claybford/ergothwack/drafts/beta/PXL_20240225_135907573.jpg

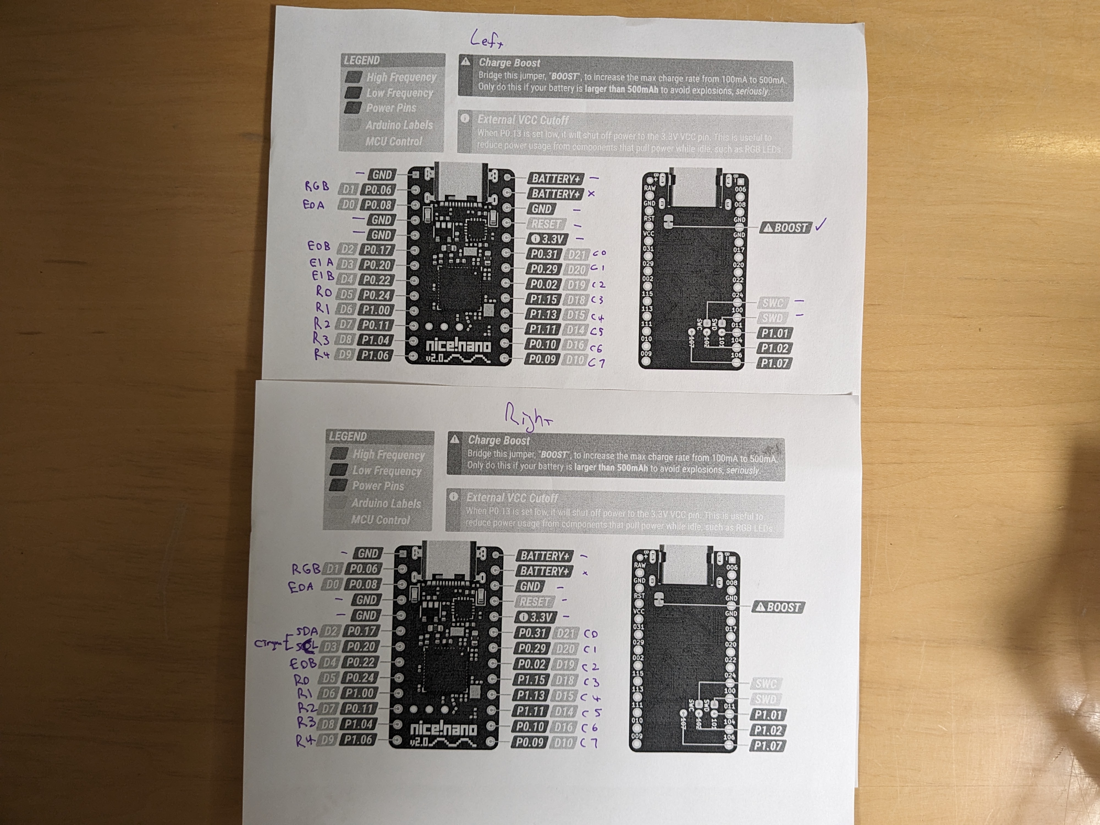
drafts/beta/PXL_20240225_135907573.jpg
