claybford/ergothwack/drafts/beta/PXL_20240225_155118894.jpg

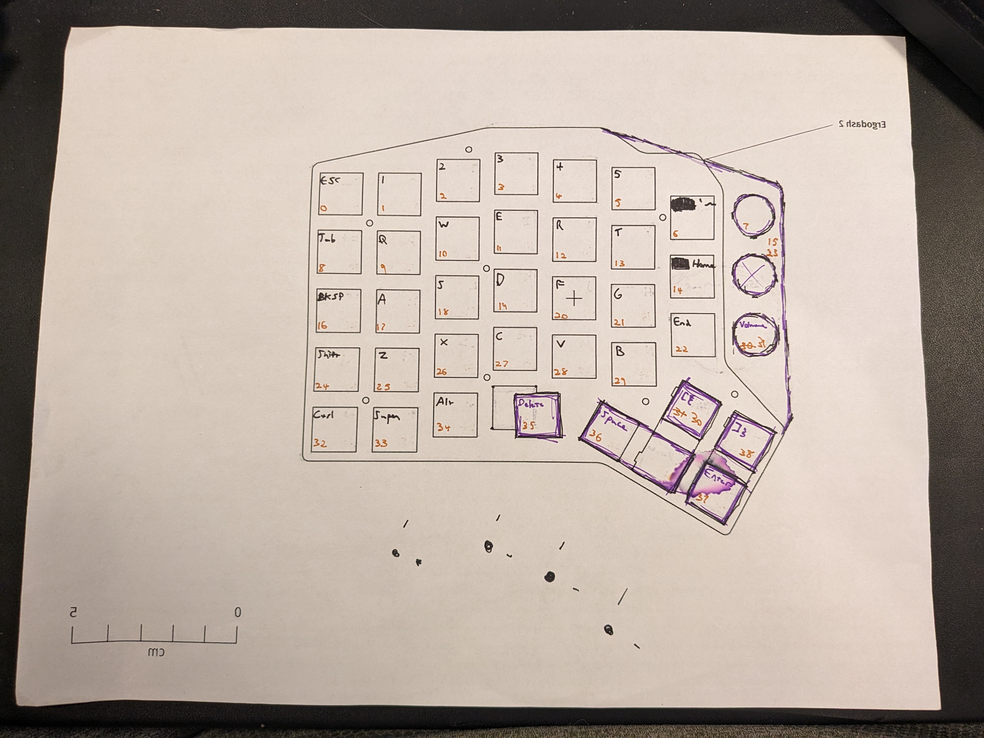
drafts/beta/PXL_20240225_155118894.jpg
