claybford/ergothwack/drafts/beta/PXL_20240225_155126803.jpg

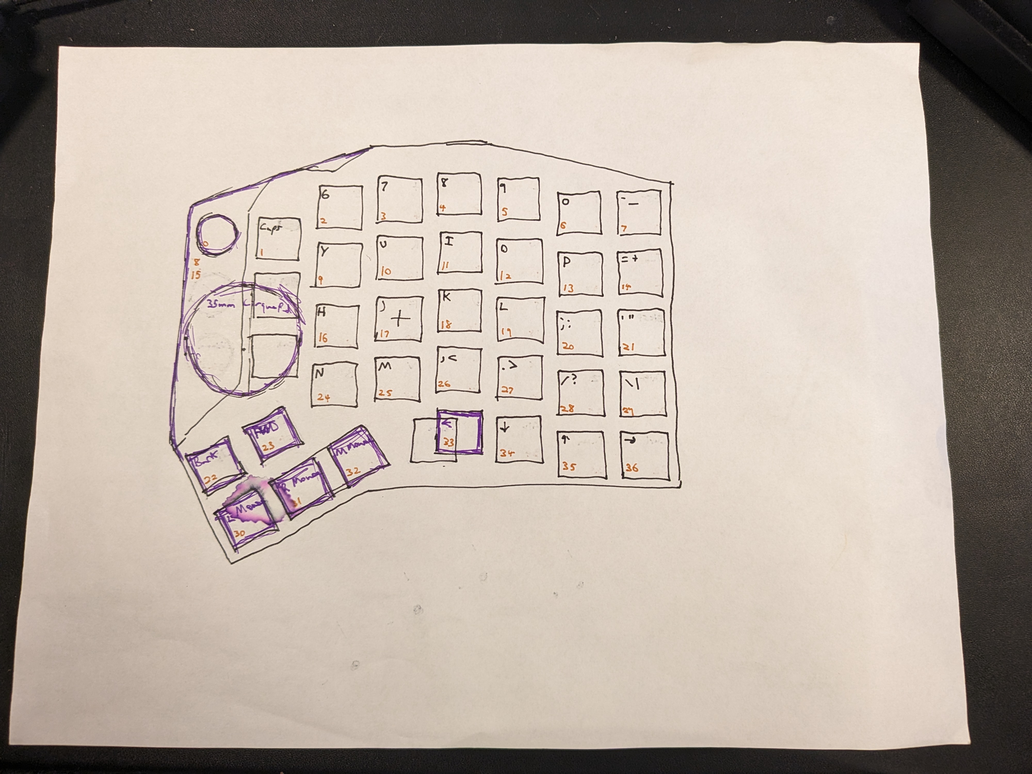
drafts/beta/PXL_20240225_155126803.jpg
