claybford/ergothwack/photos/beta/PXL_20240208_200405498.jpg

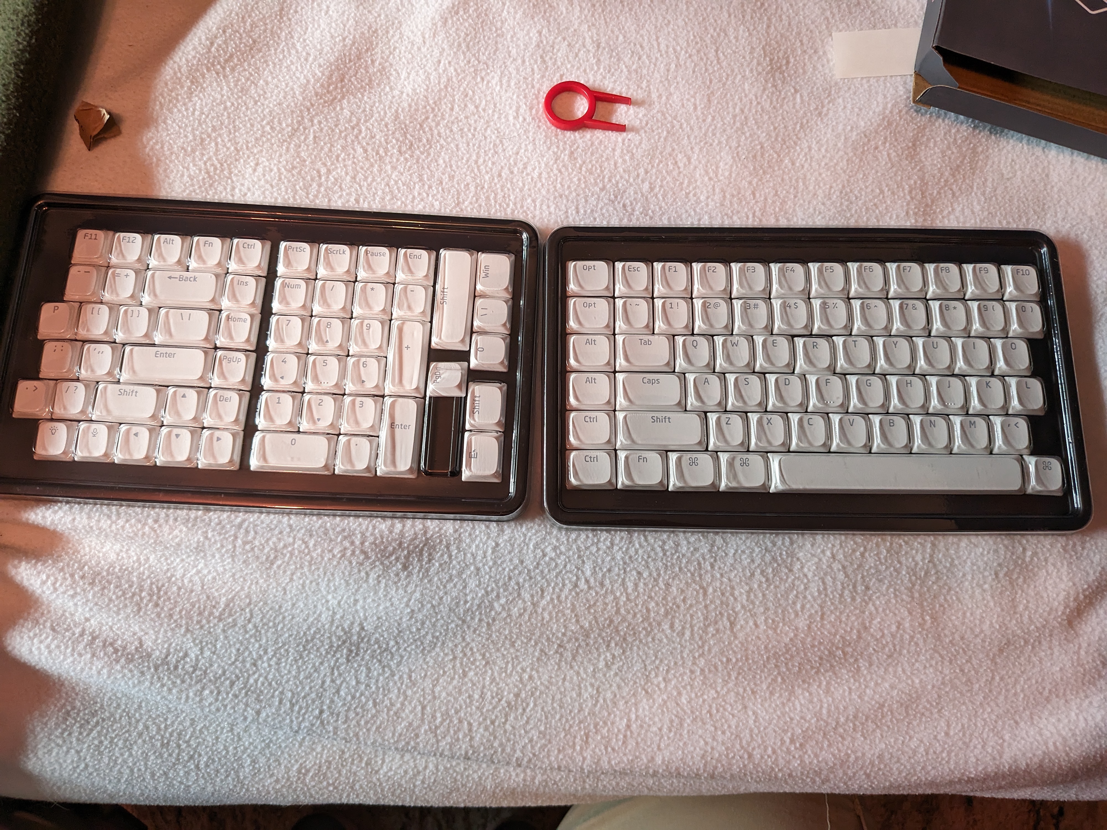
photos/beta/PXL_20240208_200405498.jpg
