claybford/ergothwack/photos/beta/PXL_20240208_202022478.jpg

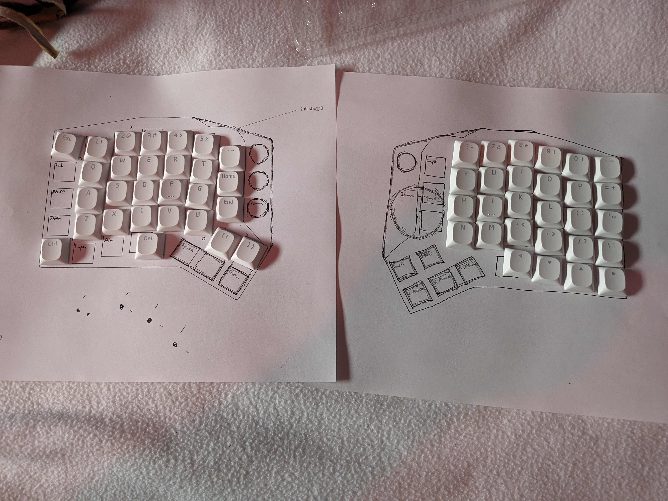
photos/beta/PXL_20240208_202022478.jpg
