claybford/ergothwack/photos/beta/PXL_20240215_032502192.jpg

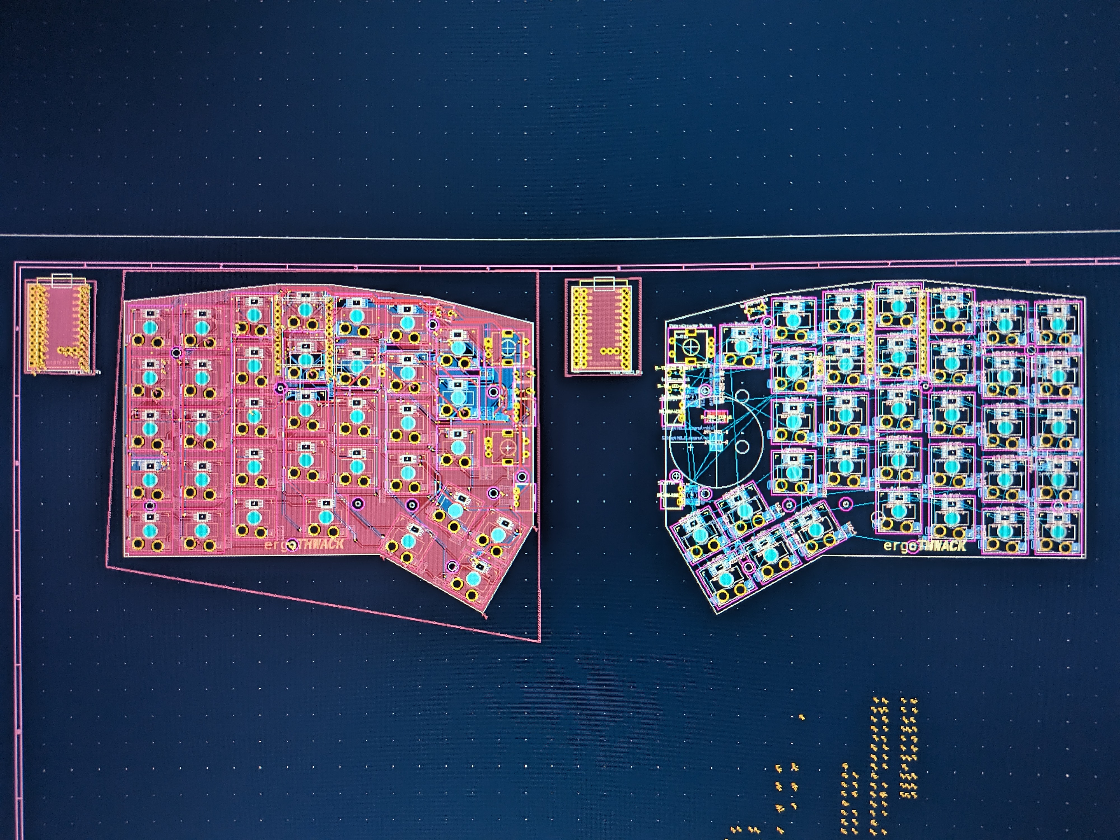
photos/beta/PXL_20240215_032502192.jpg
