claybford/ergothwack/photos/beta/PXL_20240216_200051244~2.jpg

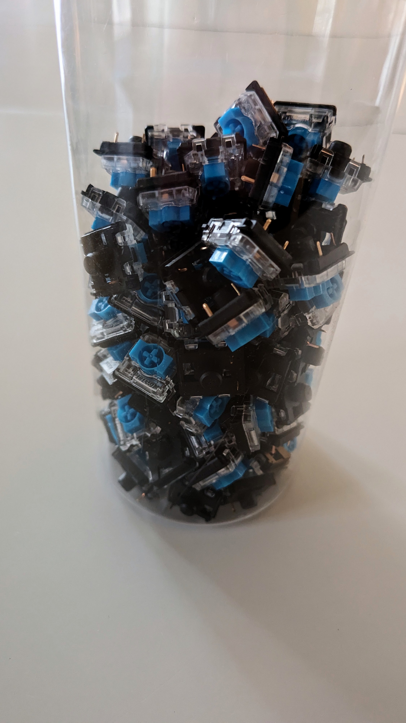
photos/beta/PXL_20240216_200051244~2.jpg
