claybford/ergothwack/photos/beta/PXL_20240217_183212310~2.jpg

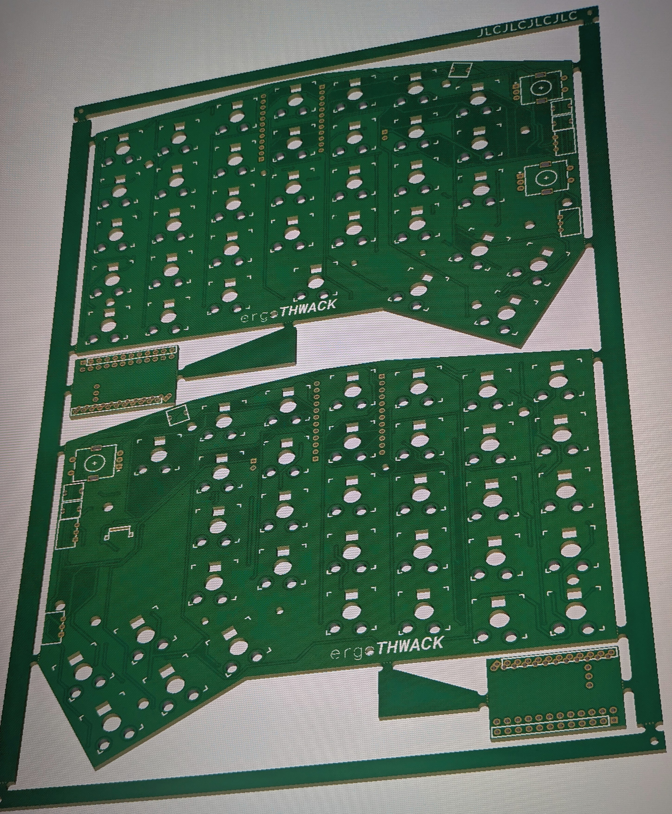
photos/beta/PXL_20240217_183212310~2.jpg
