claybford/ergothwack/photos/beta/PXL_20240222_214427850.jpg

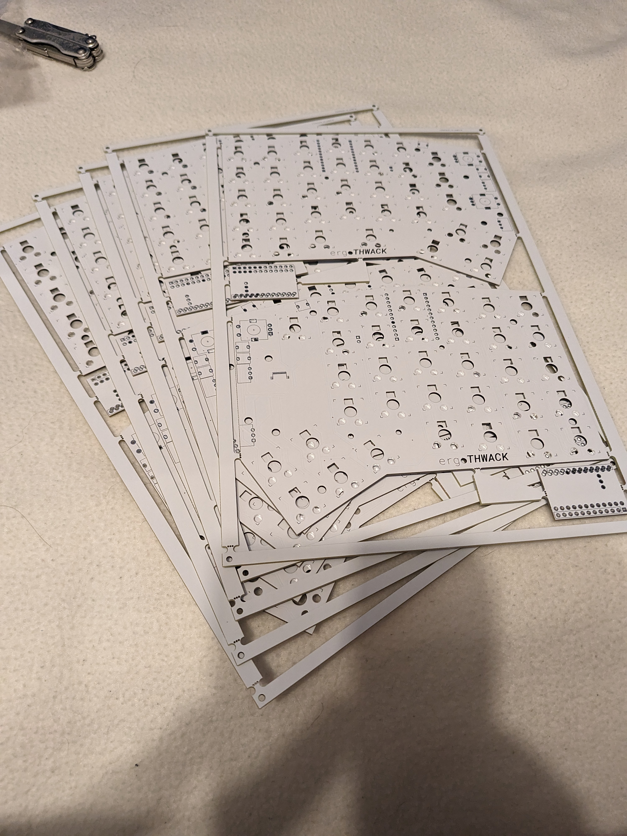
photos/beta/PXL_20240222_214427850.jpg
