claybford/ergothwack/photos/beta/PXL_20240222_214445857.jpg

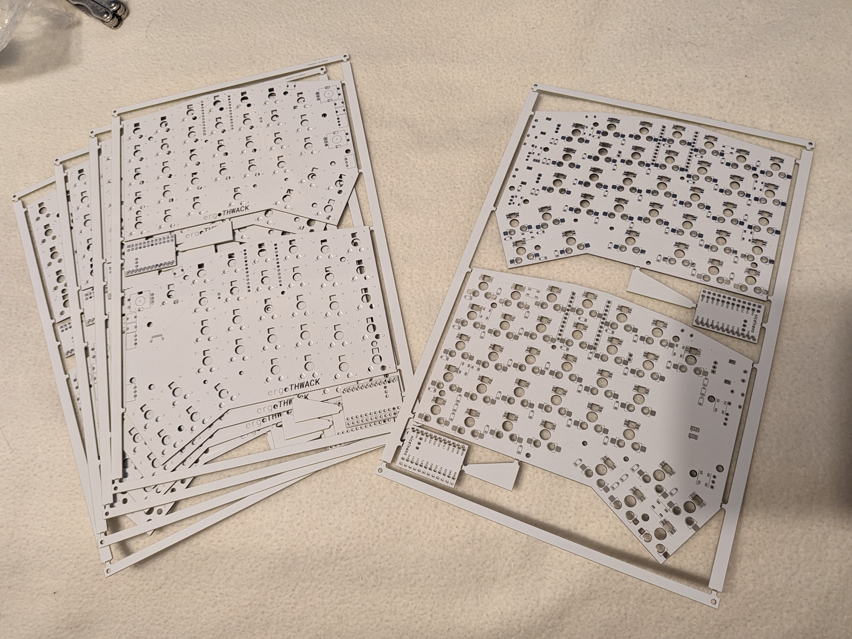
photos/beta/PXL_20240222_214445857.jpg
