claybford/ergothwack/photos/beta/PXL_20240222_214501451.jpg

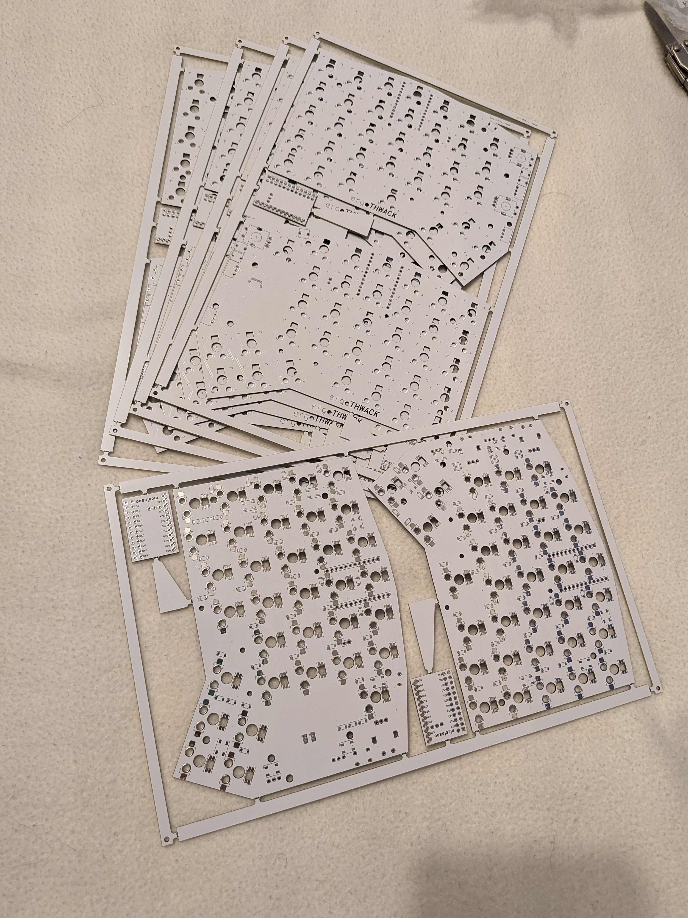
photos/beta/PXL_20240222_214501451.jpg
