claybford/ergothwack/photos/beta/PXL_20240222_214855161.jpg

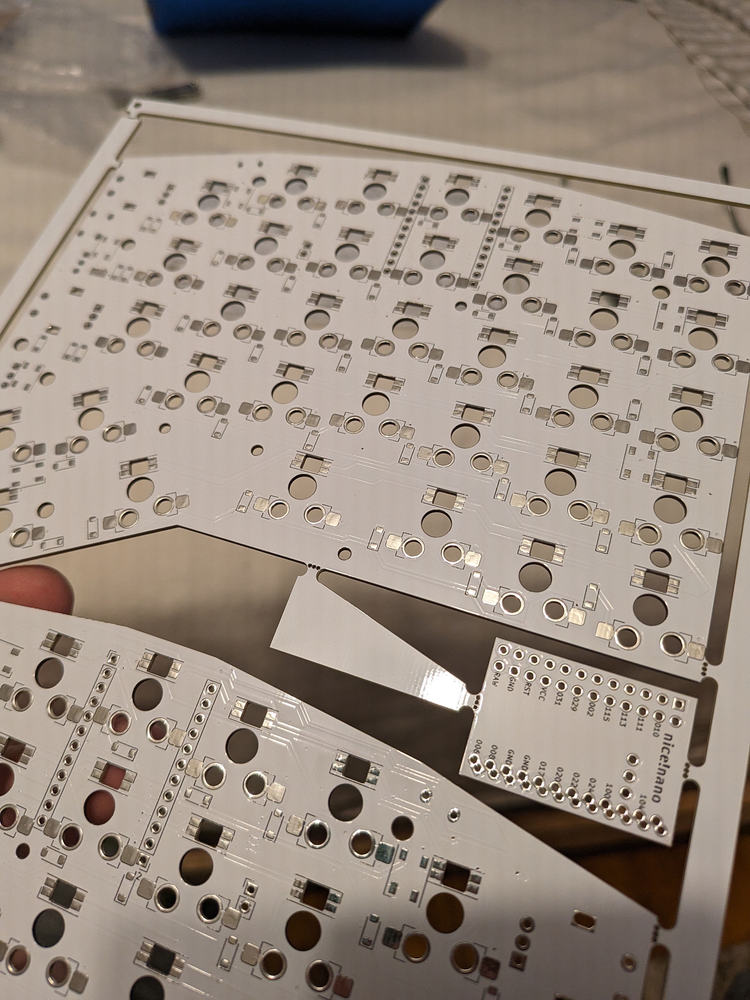
photos/beta/PXL_20240222_214855161.jpg
