claybford/ergothwack/photos/beta/PXL_20240222_214902118.jpg

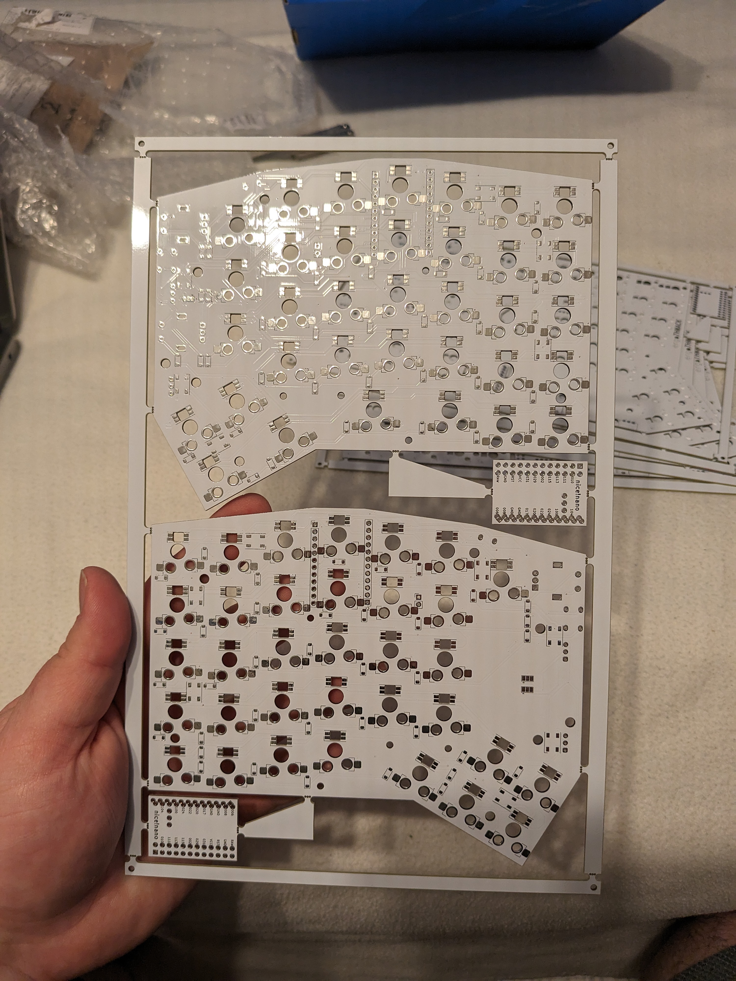
photos/beta/PXL_20240222_214902118.jpg
