claybford/ergothwack/photos/beta/PXL_20240222_214908877.jpg

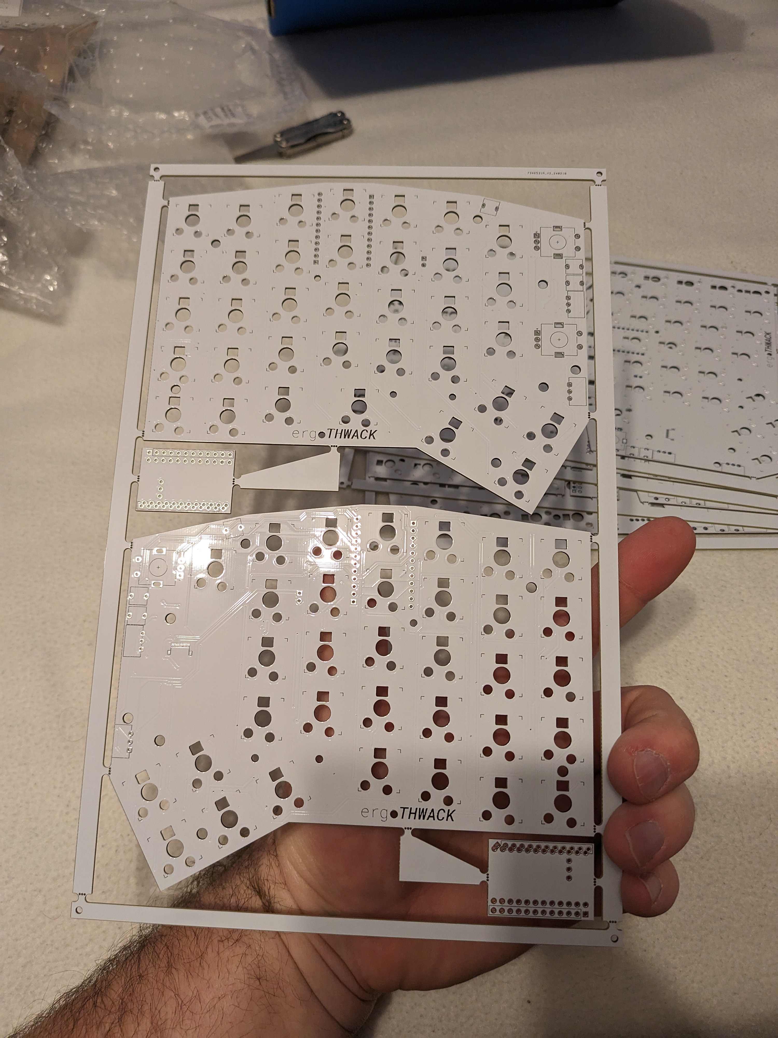
photos/beta/PXL_20240222_214908877.jpg
