claybford/ergothwack/photos/beta/PXL_20240222_215357096.jpg

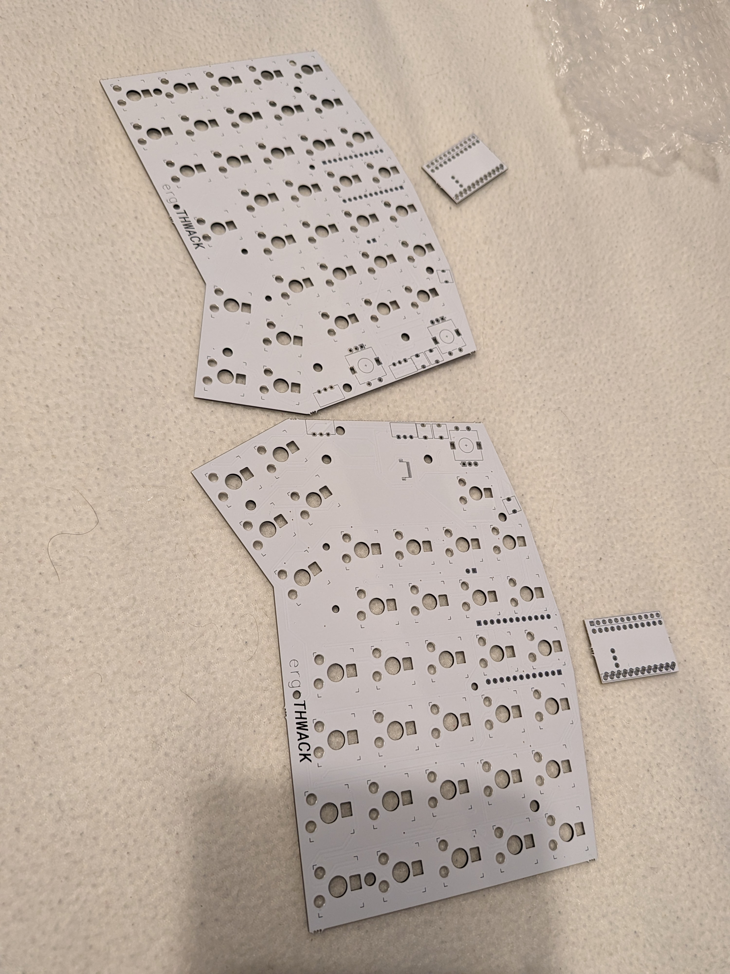
photos/beta/PXL_20240222_215357096.jpg
