claybford/ergothwack/photos/beta/PXL_20240224_054337741.jpg

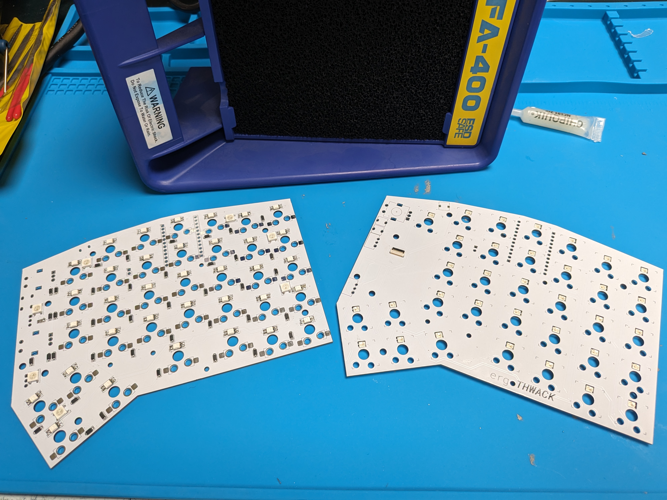
photos/beta/PXL_20240224_054337741.jpg
