claybford/ergothwack/photos/beta/PXL_20240224_054445099.jpg

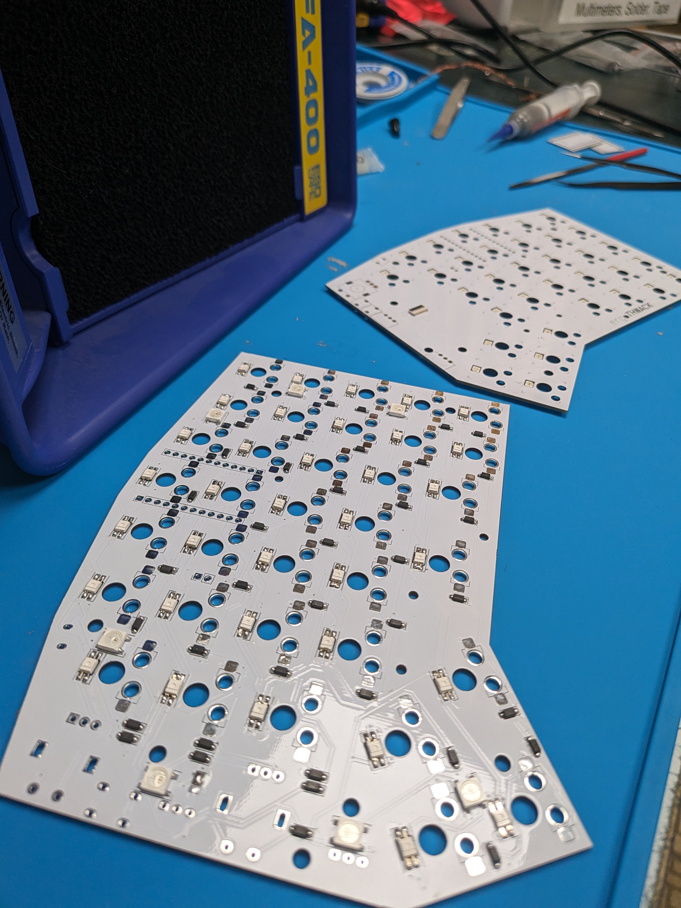
photos/beta/PXL_20240224_054445099.jpg
