claybford/ergothwack/photos/beta/PXL_20240224_054820994.jpg

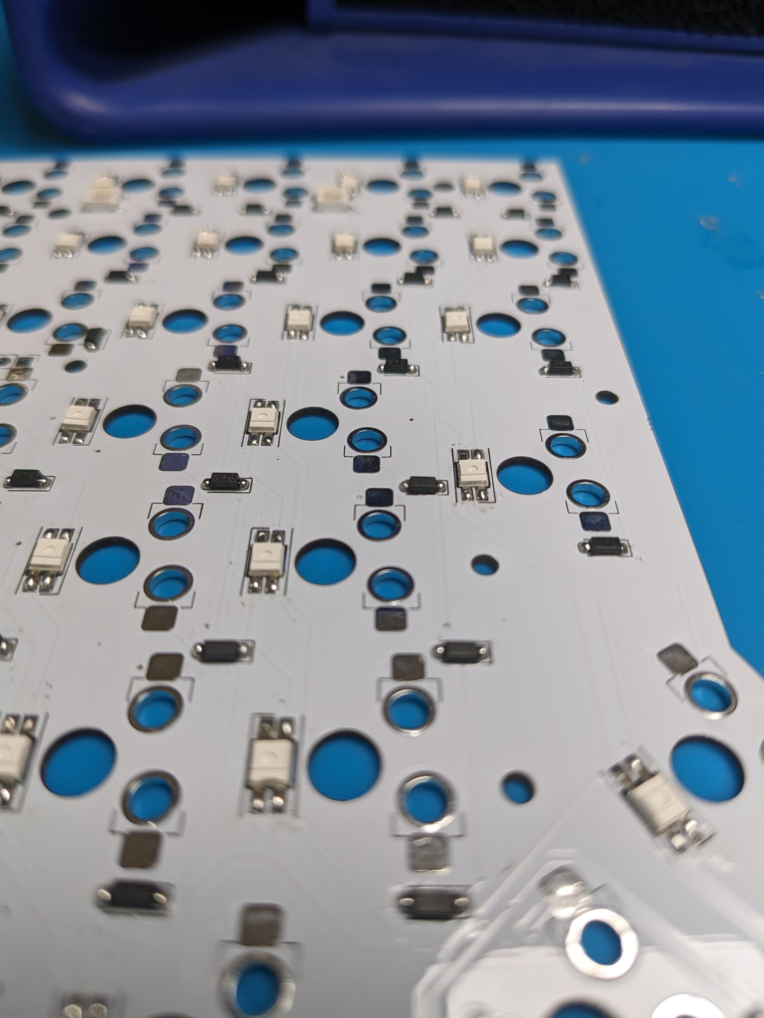
photos/beta/PXL_20240224_054820994.jpg
