claybford/ergothwack/photos/beta/PXL_20240227_215155675~2.jpg

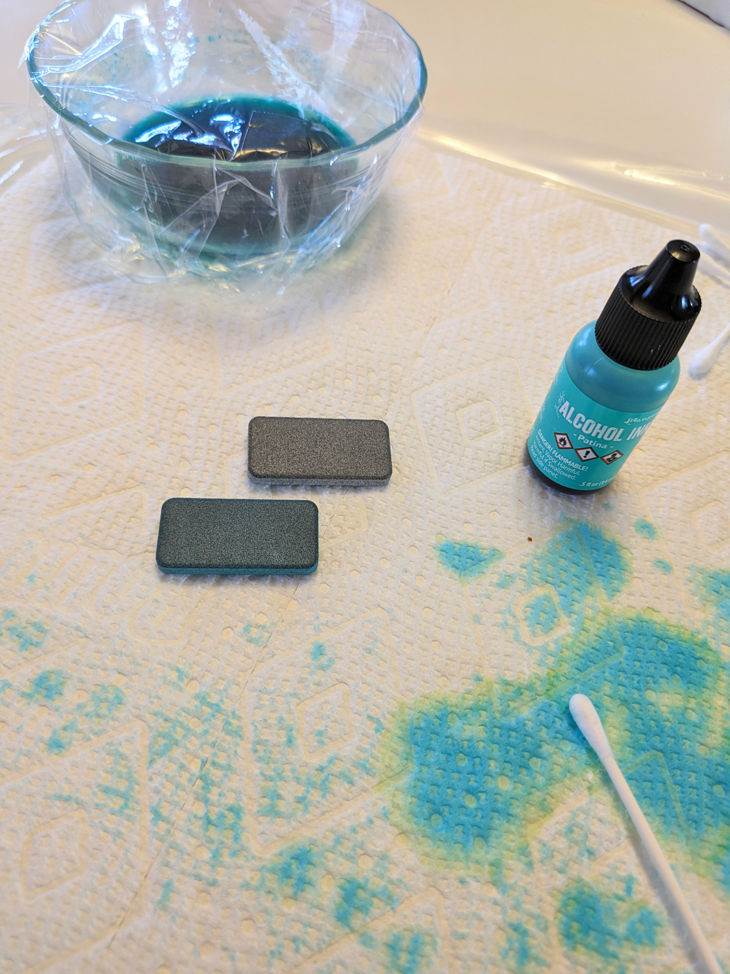
photos/beta/PXL_20240227_215155675~2.jpg
