claybford/ergothwack/photos/beta/PXL_20240301_024840404.jpg

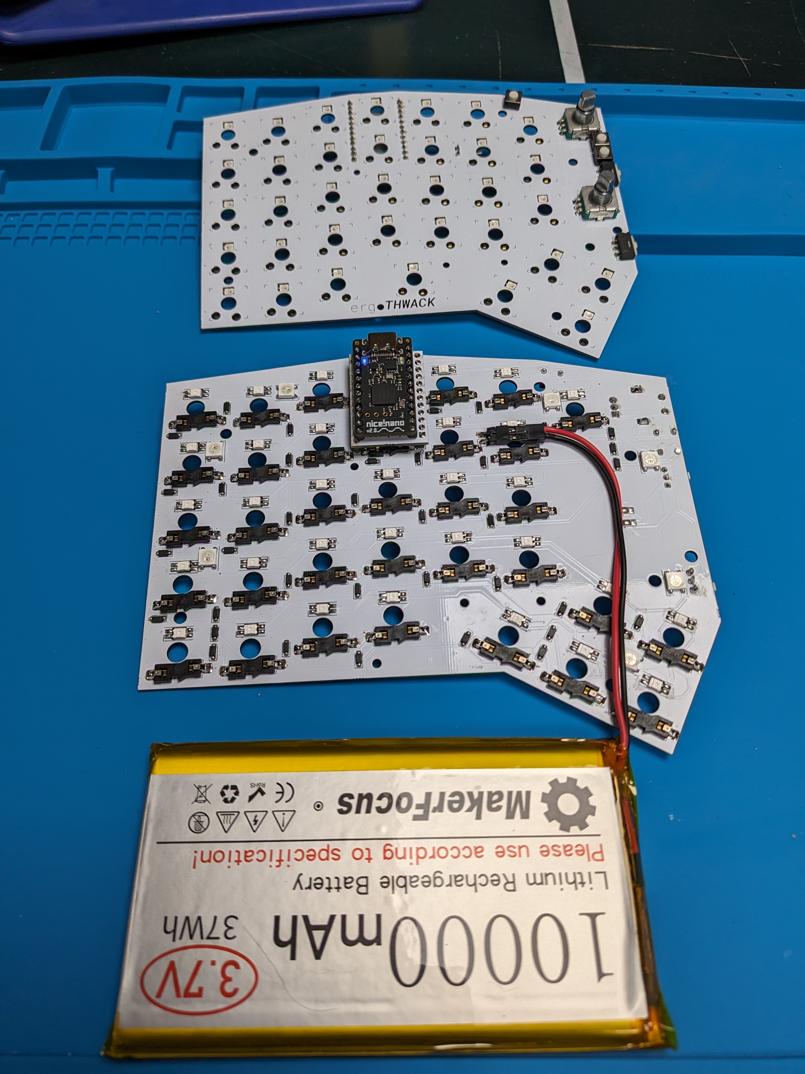
photos/beta/PXL_20240301_024840404.jpg
