claybford/ergothwack/photos/beta/PXL_20240301_025422989.jpg

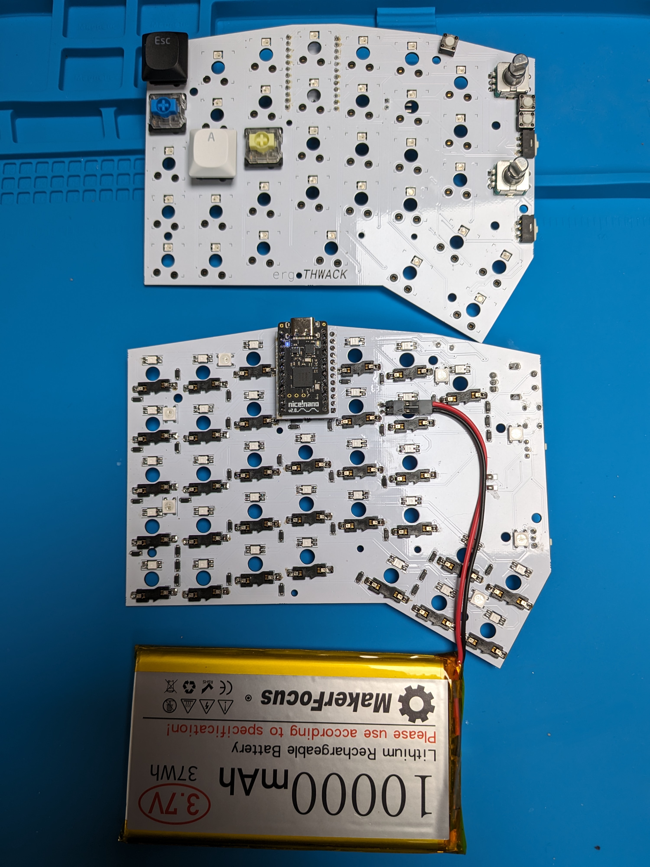
photos/beta/PXL_20240301_025422989.jpg
