claybford/ergothwack/photos/beta/PXL_20240304_221708577.jpg

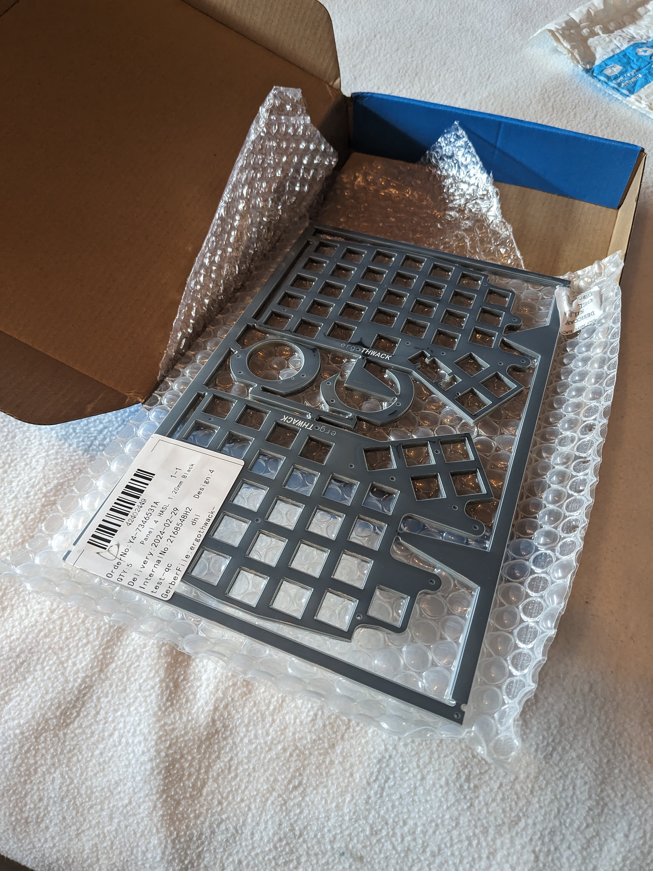
photos/beta/PXL_20240304_221708577.jpg
