claybford/ergothwack/photos/beta/PXL_20240305_060824923.jpg

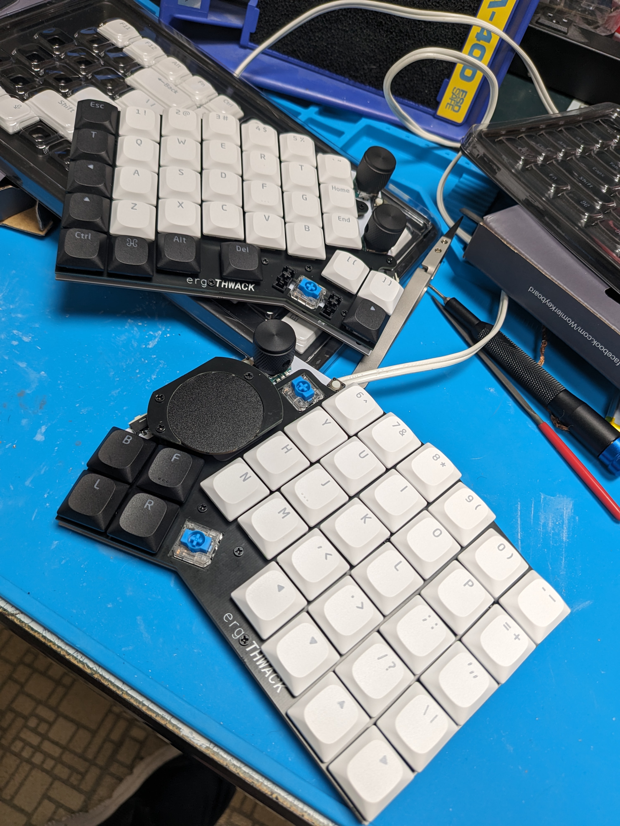
photos/beta/PXL_20240305_060824923.jpg
