claybford/ergothwack/photos/beta/PXL_20240307_211200613.jpg

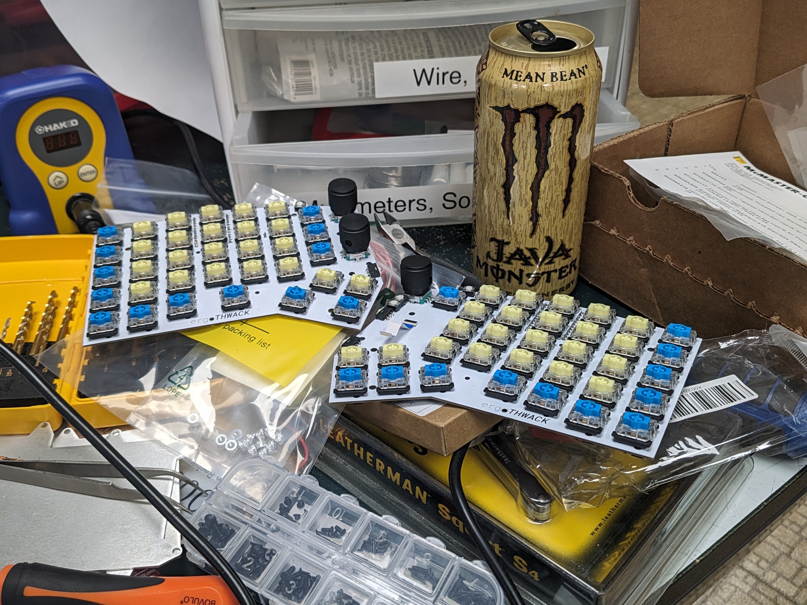
photos/beta/PXL_20240307_211200613.jpg
