claybford/ergothwack/photos/beta/PXL_20240307_211225900.jpg

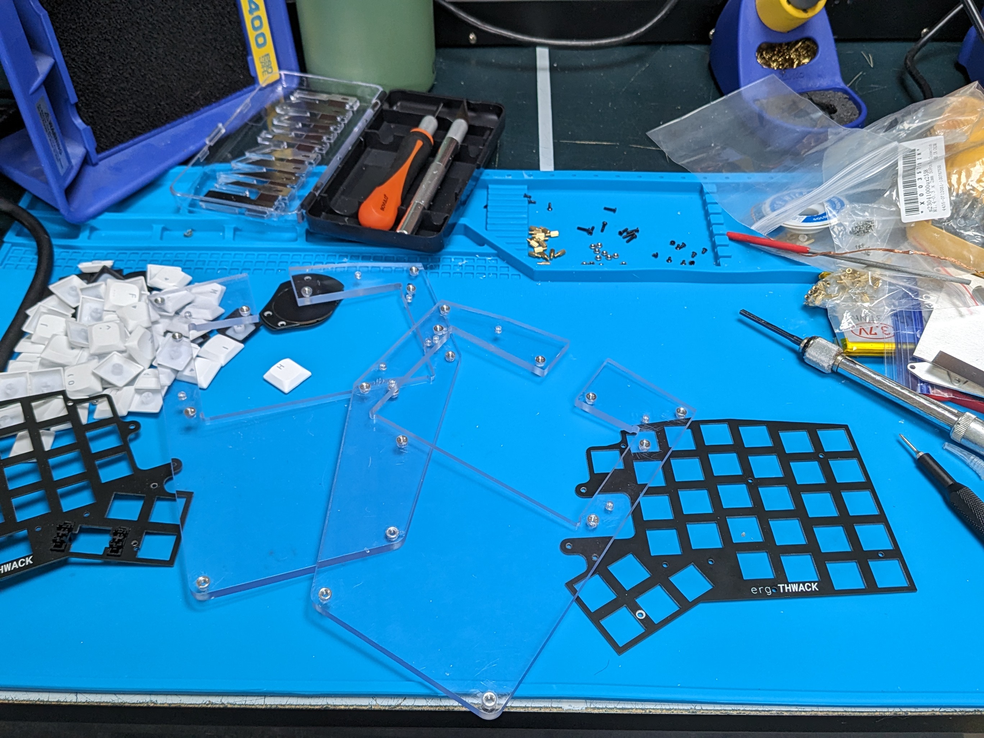
photos/beta/PXL_20240307_211225900.jpg
