claybford/ergothwack/photos/beta/PXL_20240307_215815214.jpg

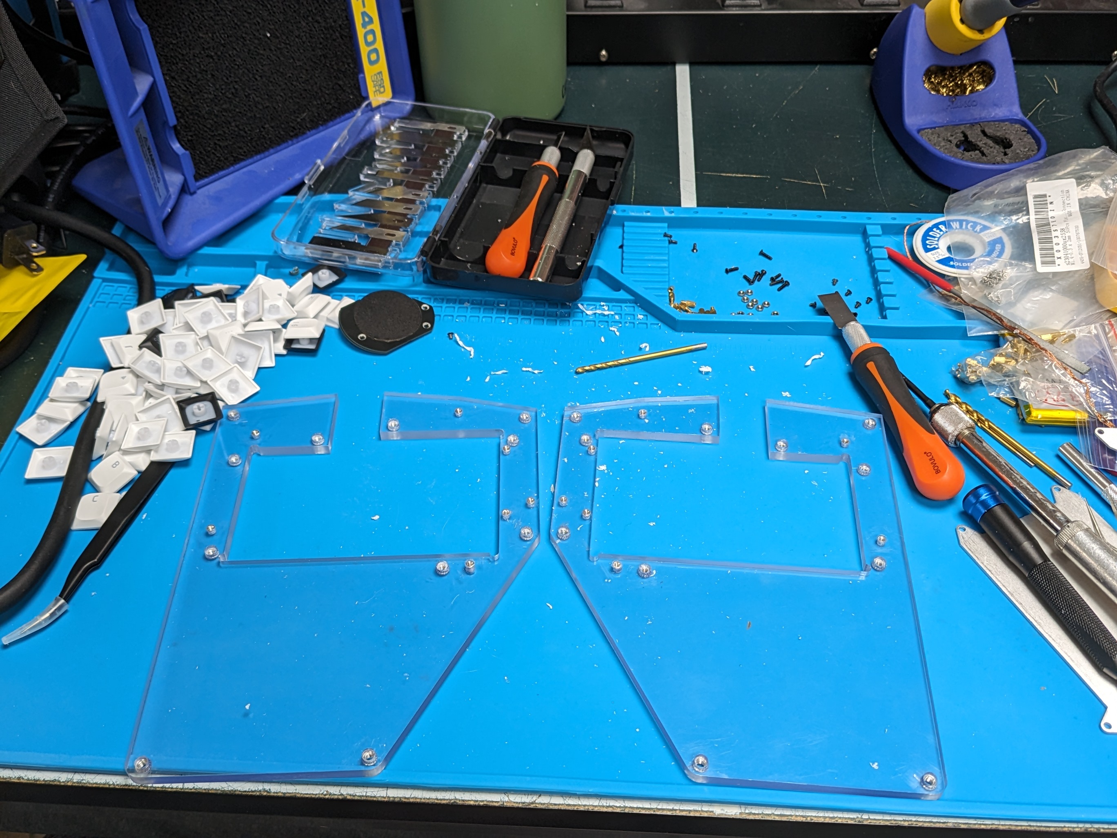
photos/beta/PXL_20240307_215815214.jpg
