claybford/ergothwack/photos/beta/PXL_20240308_015111697.jpg

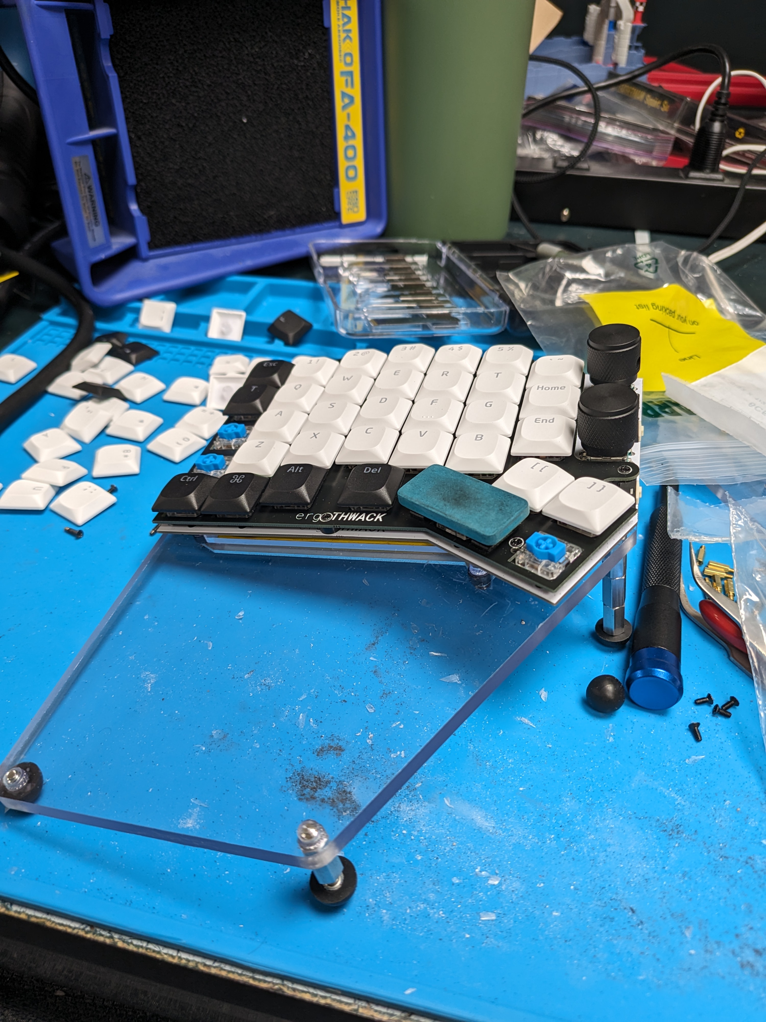
photos/beta/PXL_20240308_015111697.jpg
