claybford/ergothwack/photos/beta/PXL_20240308_015728550.jpg

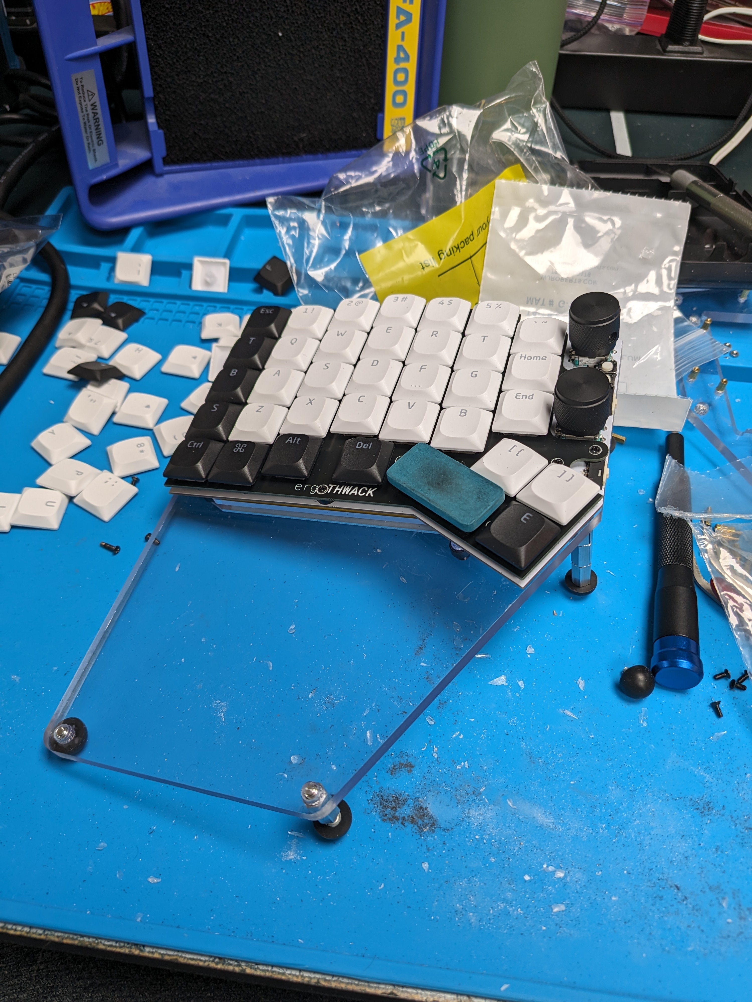
photos/beta/PXL_20240308_015728550.jpg
