claybford/ergothwack/photos/beta/PXL_20240309_044629597.jpg

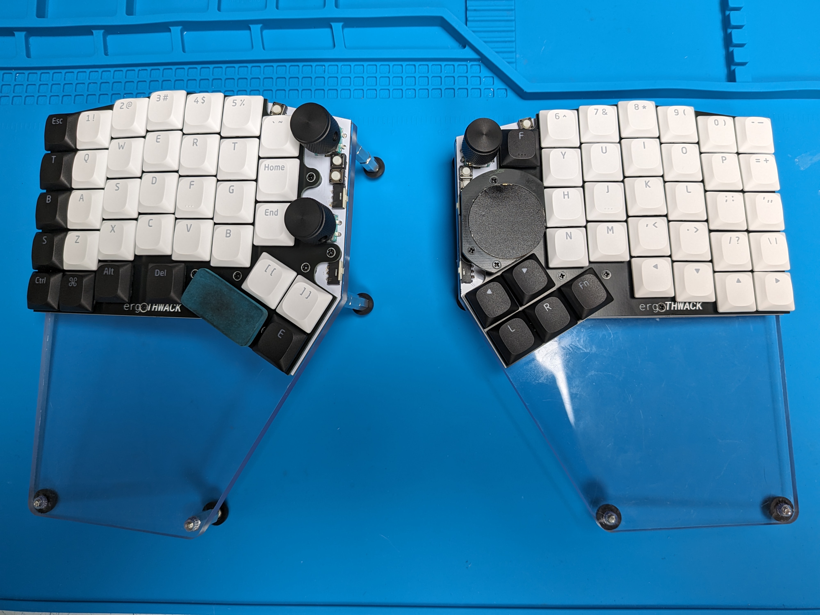
photos/beta/PXL_20240309_044629597.jpg
