claybford/ergothwack/photos/beta/PXL_20240310_044820362.jpg

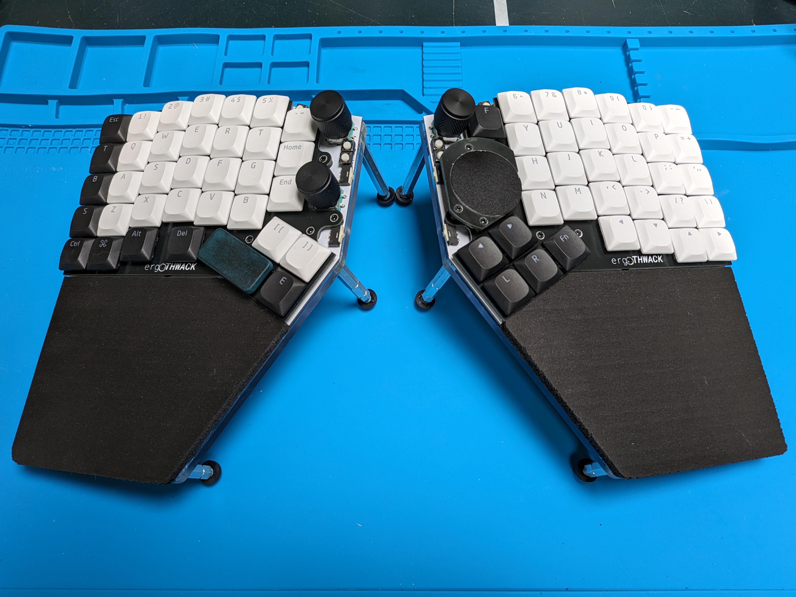
photos/beta/PXL_20240310_044820362.jpg
