claybford/ergothwack/photos/beta/PXL_20240316_183658946.jpg

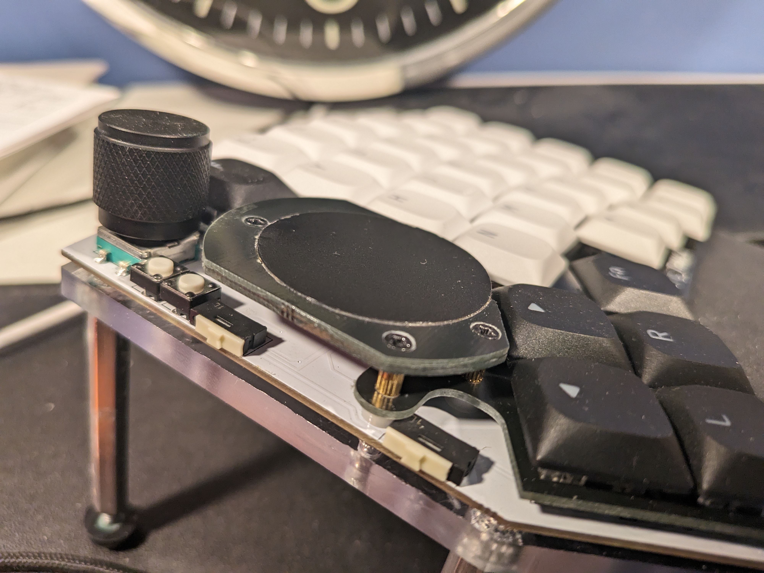
photos/beta/PXL_20240316_183658946.jpg
