claybford/ergothwack/photos/beta/PXL_20240316_183718555.jpg

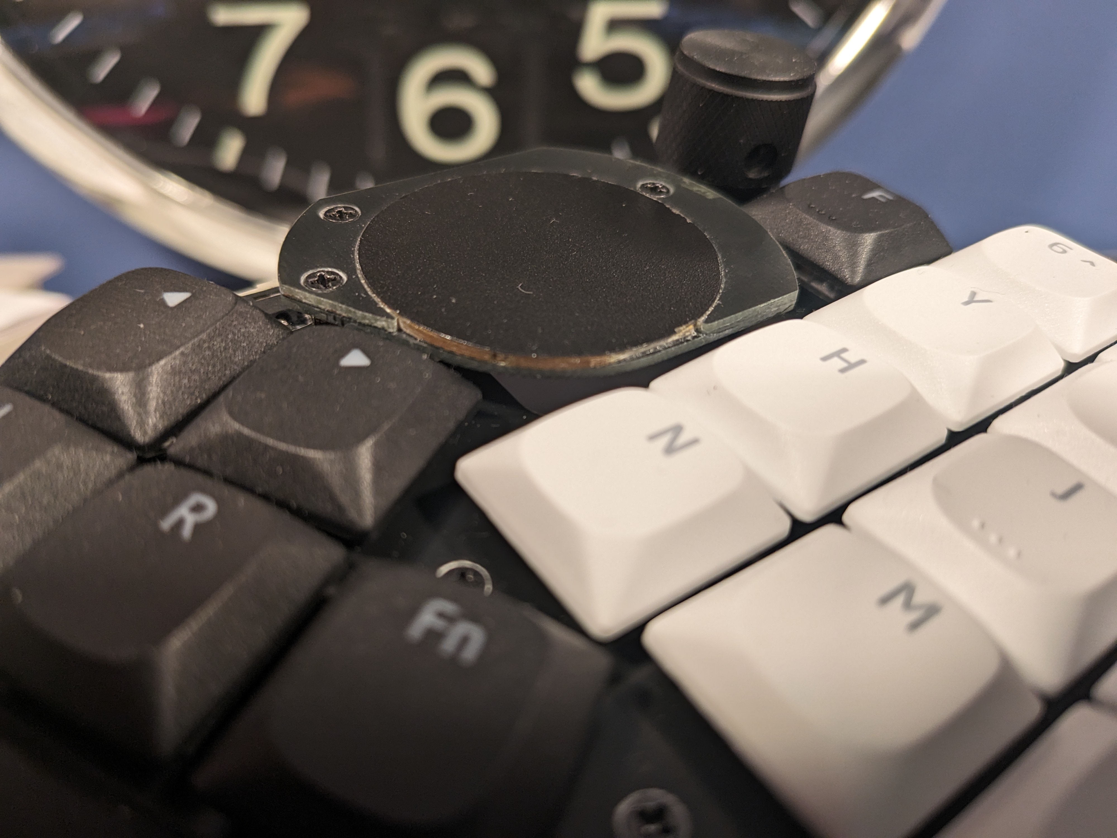
photos/beta/PXL_20240316_183718555.jpg
