claybford/ergothwack/photos/beta/PXL_20240317_012301412.jpg

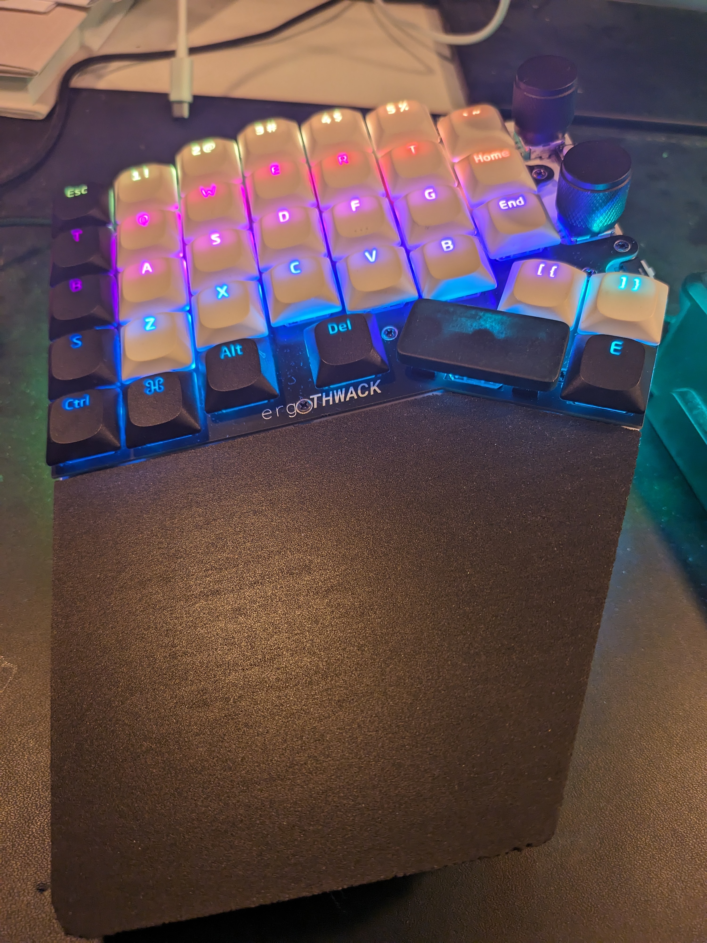
photos/beta/PXL_20240317_012301412.jpg
