claybford/ergothwack/photos/beta/PXL_20240317_012305706.jpg

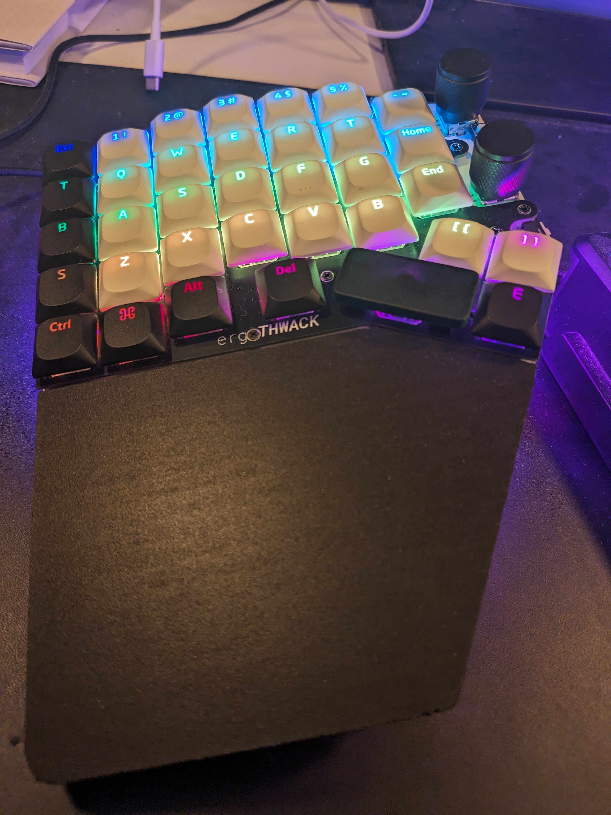
photos/beta/PXL_20240317_012305706.jpg
