claybford/ergothwack/photos/beta/PXL_20240321_230017577.jpg

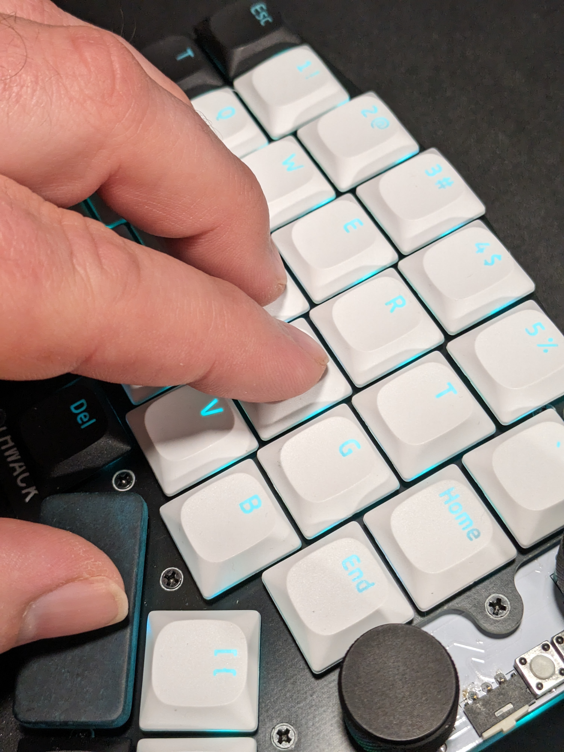
photos/beta/PXL_20240321_230017577.jpg
