claybford/ergothwack/reference documents/gateron low profile stabilizer.png

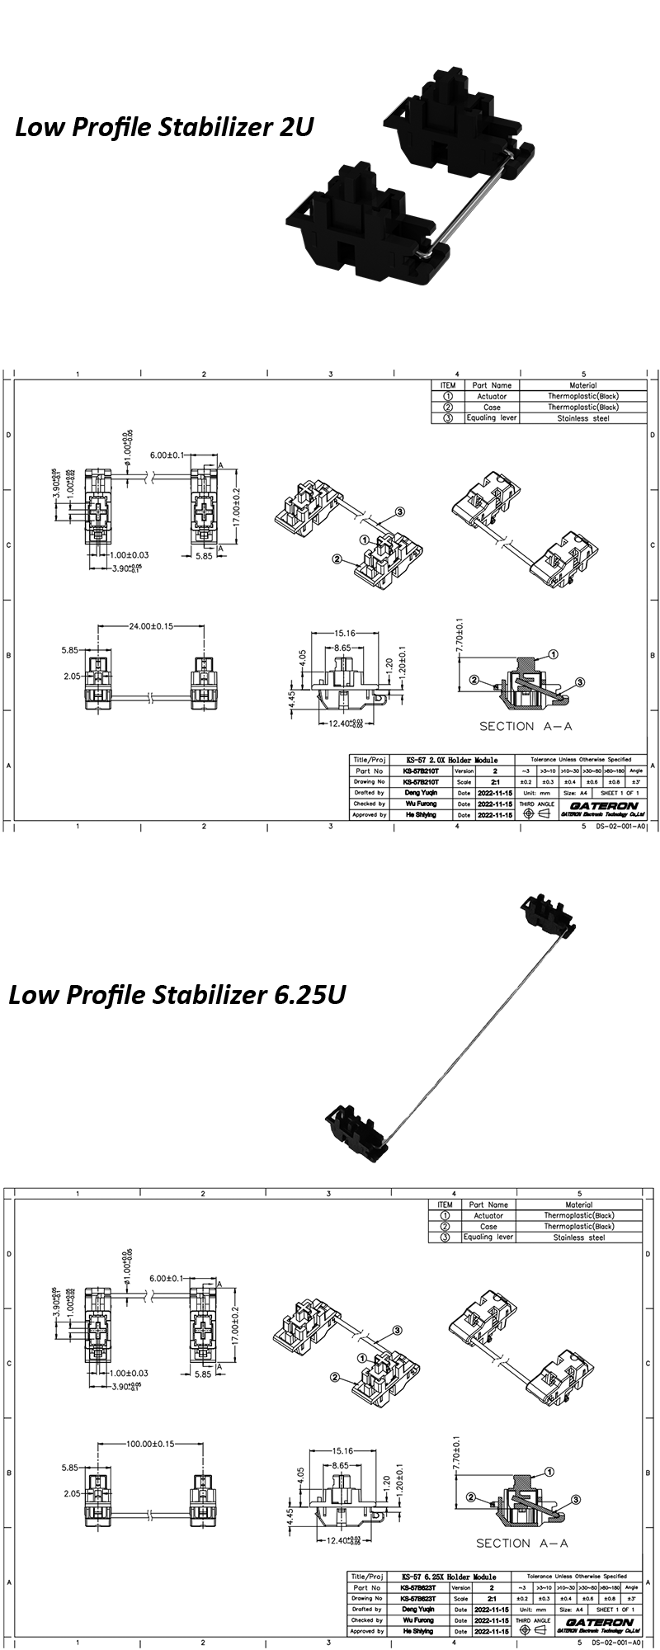
reference documents/gateron low profile stabilizer.png
