claybford/ergothwack/reference documents/Gateron low-profile hot swap socket diagram.webp

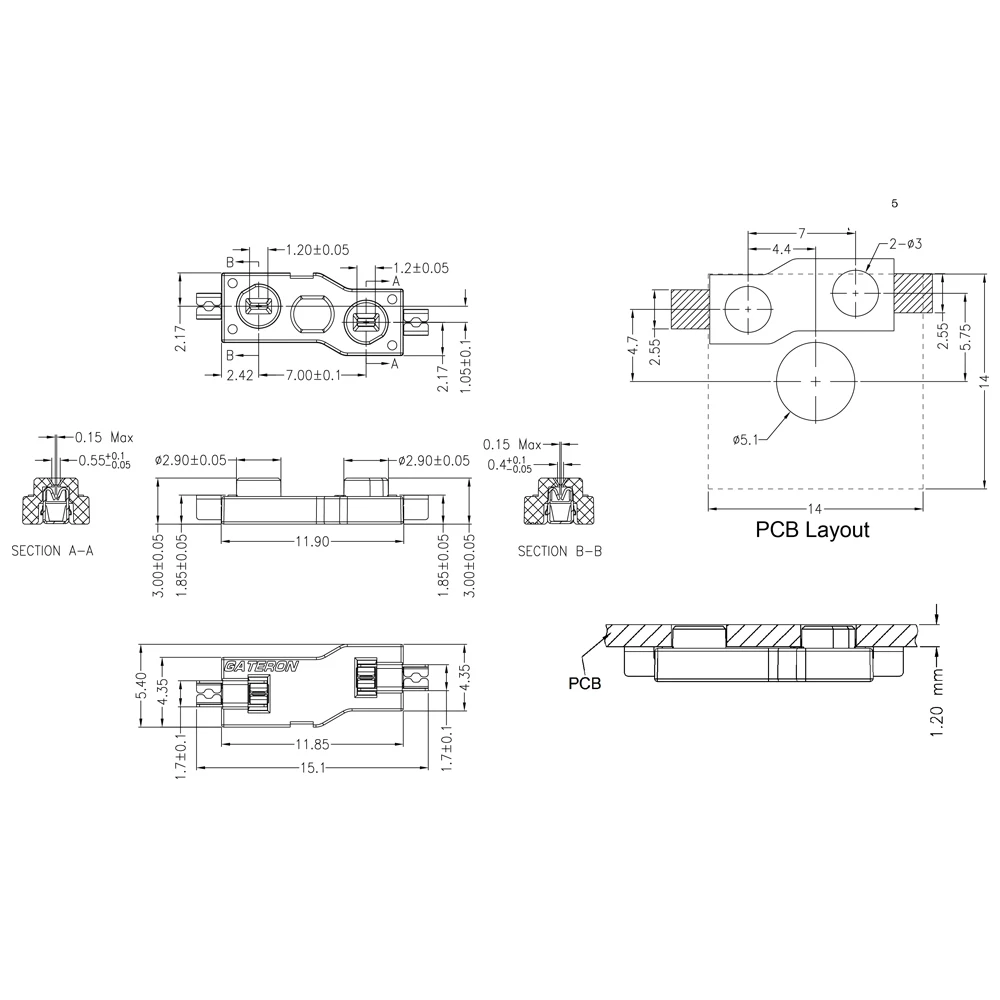
reference documents/Gateron low-profile hot swap socket diagram.webp
