claybford/ergothwack/reference documents/Gateron low-profile switch diagram ks27.webp

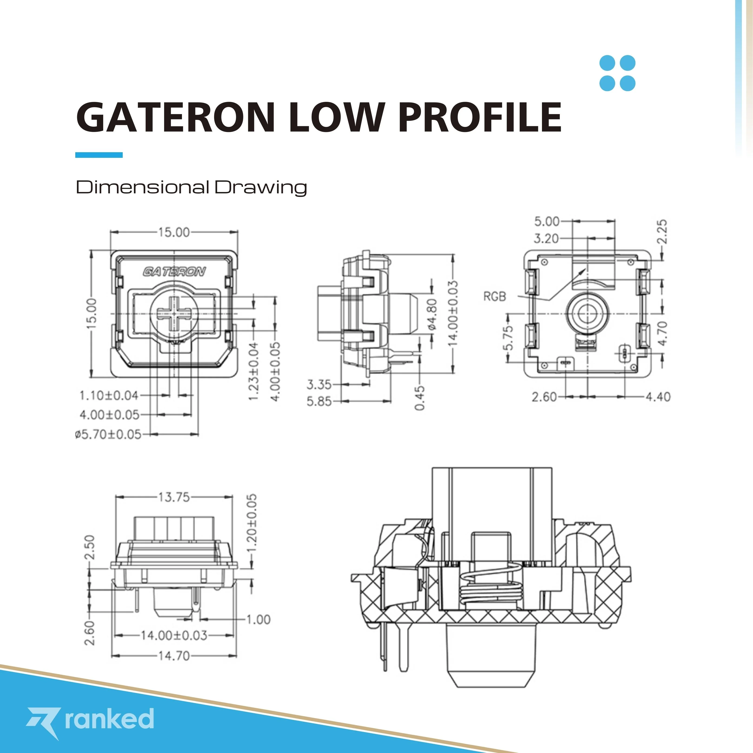
reference documents/Gateron low-profile switch diagram ks27.webp
