claybford/ergothwack/reference documents/Gateron low-profile switch diagram.jpg

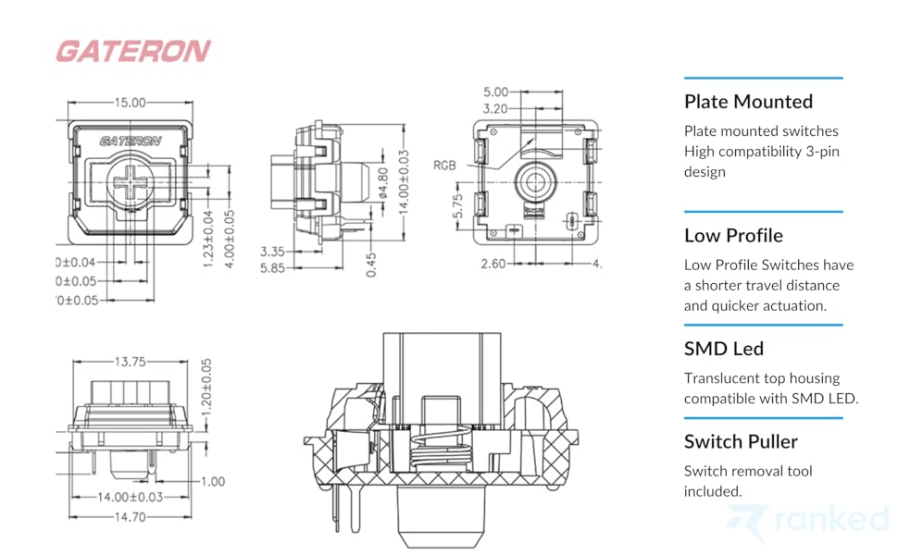
reference documents/Gateron low-profile switch diagram.jpg
