claybford/ergothwack/renders/beta/ergothwack render composite.png

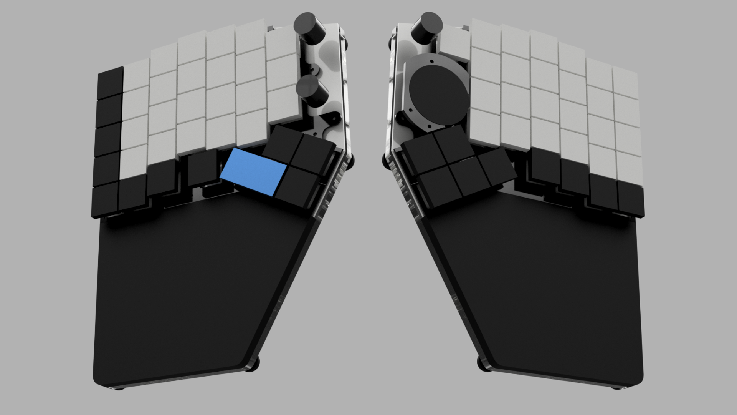
renders/beta/ergothwack render composite.png
