claybford/ergothwack/renders/beta/ergothwack right.png

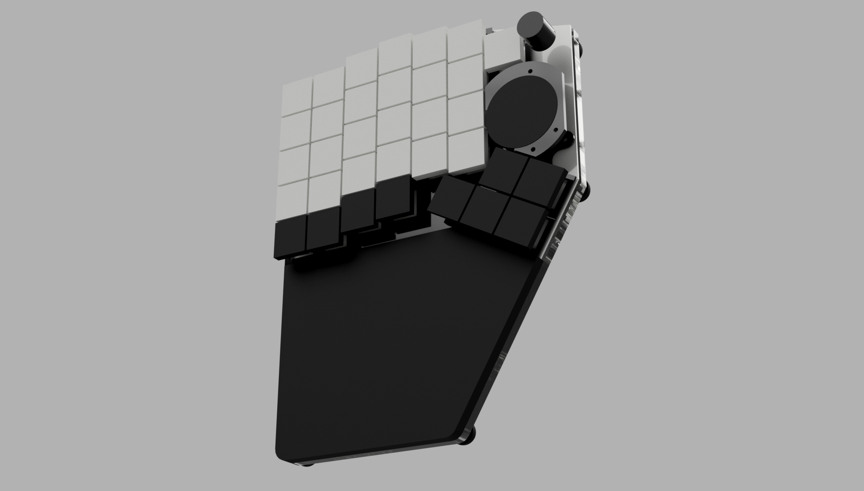
renders/beta/ergothwack right.png
