claybford/ergothwack/PCB/beta/ergothwack/ergothwack.kicad_sch

## KiCad design PCB/beta/ergothwack/ergothwack.kicad_sch (2024-03-23)

Schematic: ergothwack.kicad_sch

Parts:
J1: R-n!n-R-Adapter; PinHeader_1x12_P2.54mm_Vertical
J2: R-n!n-R-Socket; PinHeader_1x12_P2.54mm_Vertical
J3: L-n!n-R-Socket; PinHeader_1x12_P2.54mm_Vertical
J4: L-n!n-R-Adapter; PinHeader_1x12_P2.54mm_Vertical
L-BATT-CONN1: Conn_01x02_Socket; PinHeader_1x02_P2.54mm_Vertical
L-D0, L-D1, L-D2, L-D3, L-D4, L-D5, L-D6, L-D7, L-D8, L-D9, L-D10, L-D11, L-D12, L-D13, L-D14, L-D15, L-D16, L-D17, L-D18, L-D19, L-D20, L-D21, L-D22, L-D23, L-D24, L-D25, L-D26, L-D27, L-D28, L-D29, L-D30, L-D31, L-D32, L-D33, L-D34, L-D35, L-D36, L-D37, L-D38: 1N4148; D_SOD-123
L-K-LED0, L-K-LED1, L-K-LED2, L-K-LED3, L-K-LED4, L-K-LED5, L-K-LED6, L-K-LED8, L-K-LED9, L-K-LED10, L-K-LED11, L-K-LED12, L-K-LED13, L-K-LED14, L-K-LED16, L-K-LED17, L-K-LED18, L-K-LED19, L-K-LED20, L-K-LED21, L-K-LED22, L-K-LED24, L-K-LED25, L-K-LED26, L-K-LED27, L-K-LED28, L-K-LED29, L-K-LED30, L-K-LED32, L-K-LED33, L-K-LED34, L-K-LED35, L-K-LED36, L-K-LED37, L-K-LED38: YS-SK6812MINI-E
L-LED-JP1: SolderJumper_3_Bridged12; SolderJumper-3_P1.3mm_Bridged12_Pad1.0x1.5mm
L-RE0, L-RE1: RotaryEncoder_Switch; RotaryEncoder_Alps_EC11E-Switch_Vertical_H20mm
L-SW0, L-SW1, L-SW2, L-SW3, L-SW4, L-SW5, L-SW6, L-SW8, L-SW9, L-SW10, L-SW11, L-SW12, L-SW13, L-SW14, L-SW16, L-SW17, L-SW18, L-SW19, L-SW20, L-SW21, L-SW22, L-SW24, L-SW25, L-SW26, L-SW27, L-SW28, L-SW29, L-SW30, L-SW32, L-SW33, L-SW34, L-SW35, L-SW36, L-SW37, L-SW38: hot-swap-ks-33; SW_Gateron_LowProfile_HotSwap_PTH
L-SW-BATT1: SW_SPDT; CL-SA-12C4-02-SPDT-Slide-Switch
L-SW-LED1: SW_SPDT; CL-SA-12C4-02-SPDT-Slide-Switch
L-TS-LED-DOWN1: tactile-switch; TL59NF160Q-Tactile-Switch
L-TS-LED-UP1: tactile-switch; TL59NF160Q-Tactile-Switch
L-TS-RST1: tactile-switch; TL59NF160Q-Tactile-Switch
L-UG-LED0, L-UG-LED1, L-UG-LED2, L-UG-LED3, L-UG-LED4, L-UG-LED5, L-UG-LED6: WS2812B; LED_WS2812B_PLCC4_5.0x5.0mm_P3.2mm
L-n!n1: nice_nano
L-n!n-L-Adapter1: Conn_01x12_Pin; PinHeader_1x12_P2.54mm_Vertical
L-n!n-L-Socket1: Conn_01x12_Socket; PinHeader_1x12_P2.54mm_Vertical
R-BATT-CONN1: Conn_01x02_Socket; PinHeader_1x02_P2.54mm_Vertical
R-CRQ-CONN1: Conn_01x12; FPC_12
R-CRQ-JP1: SolderJumper_3_Bridged12; SolderJumper-3_P1.3mm_Bridged12_Pad1.0x1.5mm
R-D0, R-D1, R-D2, R-D3, R-D4, R-D5, R-D6, R-D7, R-D8, R-D9, R-D10, R-D11, R-D12, R-D13, R-D14, R-D15, R-D16, R-D17, R-D18, R-D19, R-D20, R-D21, R-D22, R-D23, R-D24, R-D25, R-D26, R-D27, R-D28, R-D29, R-D30, R-D31, R-D32, R-D33, R-D34, R-D35, R-D36: 1N4148; D_SOD-123
R-K-LED1, R-K-LED2, R-K-LED3, R-K-LED4, R-K-LED5, R-K-LED6, R-K-LED7, R-K-LED9, R-K-LED10, R-K-LED11, R-K-LED12, R-K-LED13, R-K-LED14, R-K-LED16, R-K-LED17, R-K-LED18, R-K-LED19, R-K-LED20, R-K-LED21, R-K-LED22, R-K-LED23, R-K-LED24, R-K-LED25, R-K-LED26, R-K-LED27, R-K-LED28, R-K-LED29, R-K-LED30, R-K-LED31, R-K-LED32, R-K-LED33, R-K-LED34, R-K-LED35, R-K-LED36: YS-SK6812MINI-E
R-LED-JP1: SolderJumper_3_Bridged12; SolderJumper-3_P1.3mm_Bridged12_Pad1.0x1.5mm
R-RE0: RotaryEncoder_Switch; RotaryEncoder_Alps_EC11E-Switch_Vertical_H20mm
R-SW1, R-SW2, R-SW3, R-SW4, R-SW5, R-SW6, R-SW7, R-SW9, R-SW10, R-SW11, R-SW12, R-SW13, R-SW14, R-SW16, R-SW17, R-SW18, R-SW19, R-SW20, R-SW21, R-SW22, R-SW23, R-SW24, R-SW25, R-SW26, R-SW27, R-SW28, R-SW29, R-SW30, R-SW31, R-SW32, R-SW33, R-SW34, R-SW35, R-SW36: hot-swap-ks-33; SW_Gateron_LowProfile_HotSwap_PTH
R-SW-BATT1: SW_SPDT; CL-SA-12C4-02-SPDT-Slide-Switch
R-SW-LED1: SW_SPDT; CL-SA-12C4-02-SPDT-Slide-Switch
R-TS-LED-DOWN1: tactile-switch; TL59NF160Q-Tactile-Switch
R-TS-LED-UP1: tactile-switch; TL59NF160Q-Tactile-Switch
R-TS-RST1: tactile-switch; TL59NF160Q-Tactile-Switch
R-UG-LED0, R-UG-LED1, R-UG-LED2, R-UG-LED3, R-UG-LED4, R-UG-LED5, R-UG-LED6: WS2812B; LED_WS2812B_PLCC4_5.0x5.0mm_P3.2mm
R-n!n1: nice_nano
R-n!n-L-Adapter1: Conn_01x12_Pin; PinHeader_1x12_P2.54mm_Vertical
R-n!n-L-Socket1: Conn_01x12_Socket; PinHeader_1x12_P2.54mm_Vertical

Connections:
+BATT: L-BATT-CONN1.1, L-LED-JP1.3 (B), L-SW-BATT1.1 (A)
GND: J3.11, L-BATT-CONN1.2, L-K-LED0.3 (VSS), L-K-LED1.3 (VSS), L-K-LED2.3 (VSS), L-K-LED3.3 (VSS), L-K-LED4.3 (VSS), L-K-LED5.3 (VSS), L-K-LED6.3 (VSS), L-K-LED8.3 (VSS), L-K-LED9.3 (VSS), L-K-LED10.3 (VSS), L-K-LED11.3 (VSS), L-K-LED12.3 (VSS), L-K-LED13.3 (VSS), L-K-LED14.3 (VSS), L-K-LED16.3 (VSS), L-K-LED17.3 (VSS), L-K-LED18.3 (VSS), L-K-LED19.3 (VSS), L-K-LED20.3 (VSS), L-K-LED21.3 (VSS), L-K-LED22.3 (VSS), L-K-LED24.3 (VSS), L-K-LED25.3 (VSS), L-K-LED26.3 (VSS), L-K-LED27.3 (VSS), L-K-LED28.3 (VSS), L-K-LED29.3 (VSS), L-K-LED30.3 (VSS), L-K-LED32.3 (VSS), L-K-LED33.3 (VSS), L-K-LED34.3 (VSS), L-K-LED35.3 (VSS), L-K-LED36.3 (VSS), L-K-LED37.3 (VSS), L-K-LED38.3 (VSS), L-RE0.C, L-RE1.C, L-TS-RST1.2, L-UG-LED0.3 (VSS), L-UG-LED1.3 (VSS), L-UG-LED2.3 (VSS), L-UG-LED3.3 (VSS), L-UG-LED4.3 (VSS), L-UG-LED5.3 (VSS), L-UG-LED6.3 (VSS), L-n!n-L-Socket1.3, L-n!n-L-Socket1.4
GND1: J4.11, L-n!n1.3 (GND), L-n!n1.4 (GND), L-n!n1.23 (GND), L-n!n-L-Adapter1.3, L-n!n-L-Adapter1.4
GND2: J1.11, R-n!n1.3 (GND), R-n!n1.4 (GND), R-n!n1.23 (GND), R-n!n-L-Adapter1.3, R-n!n-L-Adapter1.4
GNDA: J2.11, R-BATT-CONN1.2, R-CRQ-CONN1.11, R-K-LED1.3 (VSS), R-K-LED2.3 (VSS), R-K-LED3.3 (VSS), R-K-LED4.3 (VSS), R-K-LED5.3 (VSS), R-K-LED6.3 (VSS), R-K-LED7.3 (VSS), R-K-LED9.3 (VSS), R-K-LED10.3 (VSS), R-K-LED11.3 (VSS), R-K-LED12.3 (VSS), R-K-LED13.3 (VSS), R-K-LED14.3 (VSS), R-K-LED16.3 (VSS), R-K-LED17.3 (VSS), R-K-LED18.3 (VSS), R-K-LED19.3 (VSS), R-K-LED20.3 (VSS), R-K-LED21.3 (VSS), R-K-LED22.3 (VSS), R-K-LED23.3 (VSS), R-K-LED24.3 (VSS), R-K-LED25.3 (VSS), R-K-LED26.3 (VSS), R-K-LED27.3 (VSS), R-K-LED29.3 (VSS), R-K-LED30.3 (VSS), R-K-LED31.3 (VSS), R-K-LED32.3 (VSS), R-K-LED33.3 (VSS), R-K-LED34.3 (VSS), R-K-LED35.3 (VSS), R-K-LED36.3 (VSS), R-RE0.C, R-TS-RST1.2, R-UG-LED0.3 (VSS), R-UG-LED1.3 (VSS), R-UG-LED2.3 (VSS), R-UG-LED3.3 (VSS), R-UG-LED4.3 (VSS), R-UG-LED5.3 (VSS), R-UG-LED6.3 (VSS), R-n!n-L-Socket1.3, R-n!n-L-Socket1.4
L-LED: L-UG-LED0.4 (DIN), L-n!n-L-Socket1.1
L-LED-VCC: L-K-LED0.1 (VDD), L-K-LED1.1 (VDD), L-K-LED2.1 (VDD), L-K-LED3.1 (VDD), L-K-LED4.1 (VDD), L-K-LED5.1 (VDD), L-K-LED6.1 (VDD), L-K-LED8.1 (VDD), L-K-LED9.1 (VDD), L-K-LED10.1 (VDD), L-K-LED11.1 (VDD), L-K-LED12.1 (VDD), L-K-LED13.1 (VDD), L-K-LED14.1 (VDD), L-K-LED16.1 (VDD), L-K-LED17.1 (VDD), L-K-LED18.1 (VDD), L-K-LED19.1 (VDD), L-K-LED20.1 (VDD), L-K-LED21.1 (VDD), L-K-LED22.1 (VDD), L-K-LED24.1 (VDD), L-K-LED25.1 (VDD), L-K-LED26.1 (VDD), L-K-LED27.1 (VDD), L-K-LED28.1 (VDD), L-K-LED29.1 (VDD), L-K-LED30.1 (VDD), L-K-LED32.1 (VDD), L-K-LED33.1 (VDD), L-K-LED34.1 (VDD), L-K-LED35.1 (VDD), L-K-LED36.1 (VDD), L-K-LED37.1 (VDD), L-K-LED38.1 (VDD), L-SW-LED1.2 (B), L-UG-LED0.1 (VDD), L-UG-LED1.1 (VDD), L-UG-LED2.1 (VDD), L-UG-LED3.1 (VDD), L-UG-LED4.1 (VDD), L-UG-LED5.1 (VDD), L-UG-LED6.1 (VDD)
L-LED-VCC-PRESWITCH: L-LED-JP1.2 (C), L-SW-LED1.1 (A)
L-RAW: J3.12, L-SW-BATT1.2 (B)
L-RE0-A: L-RE0.A, L-n!n-L-Socket1.2
L-RE0-B: L-RE0.B, L-n!n-L-Socket1.5
L-RE1-A: L-RE1.A, L-n!n-L-Socket1.6
L-RE1-B: L-RE1.B, L-n!n-L-Socket1.7
L-col0: J3.8, L-SW0.1, L-SW8.1, L-SW16.1, L-SW24.1, L-SW32.1
L-col1: J3.7, L-SW1.1, L-SW9.1, L-SW17.1, L-SW25.1, L-SW33.1
L-col2: J3.6, L-SW2.1, L-SW10.1, L-SW18.1, L-SW26.1, L-SW34.1
L-col3: J3.5, L-SW3.1, L-SW11.1, L-SW19.1, L-SW27.1, L-SW35.1
L-col4: J3.4, L-SW4.1, L-SW12.1, L-SW20.1, L-SW28.1, L-SW36.1
L-col5: J3.3, L-SW5.1, L-SW13.1, L-SW21.1, L-SW29.1, L-SW37.1
L-col6: J3.2, L-SW6.1, L-SW14.1, L-SW22.1, L-SW30.1, L-SW38.1
L-col7: J3.1, L-RE0.S2, L-RE1.S2, L-TS-LED-DOWN1.1, L-TS-LED-UP1.1
L-reset: J3.10, L-TS-RST1.1
L-row0: L-D0.1 (K), L-D1.1 (K), L-D2.1 (K), L-D3.1 (K), L-D4.1 (K), L-D5.1 (K), L-D6.1 (K), L-D7.1 (K), L-n!n-L-Socket1.8
L-row1: L-D8.1 (K), L-D9.1 (K), L-D10.1 (K), L-D11.1 (K), L-D12.1 (K), L-D13.1 (K), L-D14.1 (K), L-D15.1 (K), L-n!n-L-Socket1.9
L-row2: L-D16.1 (K), L-D17.1 (K), L-D18.1 (K), L-D19.1 (K), L-D20.1 (K), L-D21.1 (K), L-D22.1 (K), L-D23.1 (K), L-n!n-L-Socket1.10
L-row3: L-D24.1 (K), L-D25.1 (K), L-D26.1 (K), L-D27.1 (K), L-D28.1 (K), L-D29.1 (K), L-D30.1 (K), L-D31.1 (K), L-n!n-L-Socket1.11
L-row4: L-D32.1 (K), L-D33.1 (K), L-D34.1 (K), L-D35.1 (K), L-D36.1 (K), L-D37.1 (K), L-D38.1 (K), L-n!n-L-Socket1.12
LINE: R-BATT-CONN1.1, R-CRQ-JP1.3 (B), R-LED-JP1.3 (B), R-SW-BATT1.3 (C)
unnamed: J1.1, R-n!n1.13 (NFC1/P0.09)
unnamed: J1.2, R-n!n1.14 (NFC2/P0.10)
unnamed: J1.3, R-n!n1.15 (P1.11)
unnamed: J1.4, R-n!n1.16 (P1.13)
unnamed: J1.5, R-n!n1.17 (P1.15)
unnamed: J1.6, R-n!n1.18 (AIN0/P0.02)
unnamed: J1.7, R-n!n1.19 (AIN5/P0.29)
unnamed: J1.8, R-n!n1.20 (AIN7/P0.31)
unnamed: J1.9, R-n!n1.21 (VCC)
unnamed: J1.10, R-n!n1.22 (RST)
unnamed: J1.12, R-n!n1.24 (BATIN/P0.04)
unnamed: J4.1, L-n!n1.13 (NFC1/P0.09)
unnamed: J4.2, L-n!n1.14 (NFC2/P0.10)
unnamed: J4.3, L-n!n1.15 (P1.11)
unnamed: J4.4, L-n!n1.16 (P1.13)
unnamed: J4.5, L-n!n1.17 (P1.15)
unnamed: J4.6, L-n!n1.18 (AIN0/P0.02)
unnamed: J4.7, L-n!n1.19 (AIN5/P0.29)
unnamed: J4.8, L-n!n1.20 (AIN7/P0.31)
unnamed: J4.9, L-n!n1.21 (VCC)
unnamed: J4.10, L-n!n1.22 (RST)
unnamed: J4.12, L-n!n1.24 (BATIN/P0.04)
unnamed: L-D0.2 (A), L-SW0.2
unnamed: L-D1.2 (A), L-SW1.2
unnamed: L-D2.2 (A), L-SW2.2
unnamed: L-D3.2 (A), L-SW3.2
unnamed: L-D4.2 (A), L-SW4.2
unnamed: L-D5.2 (A), L-SW5.2
unnamed: L-D6.2 (A), L-SW6.2
unnamed: L-D7.2 (A), L-RE0.S1
unnamed: L-D8.2 (A), L-SW8.2
unnamed: L-D9.2 (A), L-SW9.2
unnamed: L-D10.2 (A), L-SW10.2
unnamed: L-D11.2 (A), L-SW11.2
unnamed: L-D12.2 (A), L-SW12.2
unnamed: L-D13.2 (A), L-SW13.2
unnamed: L-D14.2 (A), L-SW14.2
unnamed: L-D15.2 (A), L-TS-LED-UP1.2
unnamed: L-D16.2 (A), L-SW16.2
unnamed: L-D17.2 (A), L-SW17.2
unnamed: L-D18.2 (A), L-SW18.2
unnamed: L-D19.2 (A), L-SW19.2
unnamed: L-D20.2 (A), L-SW20.2
unnamed: L-D21.2 (A), L-SW21.2
unnamed: L-D22.2 (A), L-SW22.2
unnamed: L-D23.2 (A), L-TS-LED-DOWN1.2
unnamed: L-D24.2 (A), L-SW24.2
unnamed: L-D25.2 (A), L-SW25.2
unnamed: L-D26.2 (A), L-SW26.2
unnamed: L-D27.2 (A), L-SW27.2
unnamed: L-D28.2 (A), L-SW28.2
unnamed: L-D29.2 (A), L-SW29.2
unnamed: L-D30.2 (A), L-SW30.2
unnamed: L-D31.2 (A), L-RE1.S1
unnamed: L-D32.2 (A), L-SW32.2
unnamed: L-D33.2 (A), L-SW33.2
unnamed: L-D34.2 (A), L-SW34.2
unnamed: L-D35.2 (A), L-SW35.2
unnamed: L-D36.2 (A), L-SW36.2
unnamed: L-D37.2 (A), L-SW37.2
unnamed: L-D38.2 (A), L-SW38.2
unnamed: L-K-LED0.4 (DIN), L-K-LED1.2 (DOUT)
unnamed: L-K-LED1.4 (DIN), L-K-LED2.2 (DOUT)
unnamed: L-K-LED2.4 (DIN), L-K-LED3.2 (DOUT)
unnamed: L-K-LED3.4 (DIN), L-K-LED4.2 (DOUT)
unnamed: L-K-LED4.4 (DIN), L-K-LED5.2 (DOUT)
unnamed: L-K-LED5.4 (DIN), L-K-LED6.2 (DOUT)
unnamed: L-K-LED8.2 (DOUT), L-K-LED9.4 (DIN)
unnamed: L-K-LED10.2 (DOUT), L-K-LED11.4 (DIN)
unnamed: L-K-LED9.2 (DOUT), L-K-LED10.4 (DIN)
unnamed: L-K-LED11.2 (DOUT), L-K-LED12.4 (DIN)
unnamed: L-K-LED12.2 (DOUT), L-K-LED13.4 (DIN)
unnamed: L-K-LED13.2 (DOUT), L-K-LED14.4 (DIN)
unnamed: L-K-LED6.4 (DIN), L-K-LED14.2 (DOUT)
unnamed: L-K-LED8.4 (DIN), L-K-LED16.2 (DOUT)
unnamed: L-K-LED16.4 (DIN), L-K-LED17.2 (DOUT)
unnamed: L-K-LED17.4 (DIN), L-K-LED18.2 (DOUT)
unnamed: L-K-LED18.4 (DIN), L-K-LED19.2 (DOUT)
unnamed: L-K-LED19.4 (DIN), L-K-LED20.2 (DOUT)
unnamed: L-K-LED20.4 (DIN), L-K-LED21.2 (DOUT)
unnamed: L-K-LED21.4 (DIN), L-K-LED22.2 (DOUT)
unnamed: L-K-LED22.4 (DIN), L-K-LED30.2 (DOUT)
unnamed: L-K-LED24.2 (DOUT), L-K-LED25.4 (DIN)
unnamed: L-K-LED24.4 (DIN), L-K-LED32.2 (DOUT)
unnamed: L-K-LED25.2 (DOUT), L-K-LED26.4 (DIN)
unnamed: L-K-LED26.2 (DOUT), L-K-LED27.4 (DIN)
unnamed: L-K-LED27.2 (DOUT), L-K-LED28.4 (DIN)
unnamed: L-K-LED28.2 (DOUT), L-K-LED29.4 (DIN)
unnamed: L-K-LED29.2 (DOUT), L-K-LED30.4 (DIN)
unnamed: L-K-LED32.4 (DIN), L-K-LED33.2 (DOUT)
unnamed: L-K-LED33.4 (DIN), L-K-LED34.2 (DOUT)
unnamed: L-K-LED34.4 (DIN), L-K-LED35.2 (DOUT)
unnamed: L-K-LED35.4 (DIN), L-K-LED36.2 (DOUT)
unnamed: L-K-LED36.4 (DIN), L-K-LED37.2 (DOUT)
unnamed: L-K-LED37.4 (DIN), L-K-LED38.2 (DOUT)
unnamed: L-K-LED38.4 (DIN), L-UG-LED6.2 (DOUT)
unnamed: L-UG-LED0.2 (DOUT), L-UG-LED1.4 (DIN)
unnamed: L-UG-LED1.2 (DOUT), L-UG-LED2.4 (DIN)
unnamed: L-UG-LED2.2 (DOUT), L-UG-LED3.4 (DIN)
unnamed: L-UG-LED3.2 (DOUT), L-UG-LED4.4 (DIN)
unnamed: L-UG-LED4.2 (DOUT), L-UG-LED5.4 (DIN)
unnamed: L-UG-LED5.2 (DOUT), L-UG-LED6.4 (DIN)
unnamed: L-n!n1.1 (TX0/P0.06), L-n!n-L-Adapter1.1
unnamed: L-n!n1.2 (RX1/P0.08), L-n!n-L-Adapter1.2
unnamed: L-n!n1.5 (P0.17), L-n!n-L-Adapter1.5
unnamed: L-n!n1.6 (P0.20), L-n!n-L-Adapter1.6
unnamed: L-n!n1.7 (P0.22), L-n!n-L-Adapter1.7
unnamed: L-n!n1.8 (P0.24), L-n!n-L-Adapter1.8
unnamed: L-n!n1.9 (P1.00), L-n!n-L-Adapter1.9
unnamed: L-n!n1.10 (P0.11), L-n!n-L-Adapter1.10
unnamed: L-n!n1.11 (P1.04), L-n!n-L-Adapter1.11
unnamed: L-n!n1.12 (P1.06), L-n!n-L-Adapter1.12
unnamed: R-D0.2 (A), R-RE0.S1
unnamed: R-D1.2 (A), R-SW1.2
unnamed: R-D2.2 (A), R-SW2.2
unnamed: R-D3.2 (A), R-SW3.2
unnamed: R-D4.2 (A), R-SW4.2
unnamed: R-D5.2 (A), R-SW5.2
unnamed: R-D6.2 (A), R-SW6.2
unnamed: R-D7.2 (A), R-SW7.2
unnamed: R-D8.2 (A), R-TS-LED-UP1.2
unnamed: R-D9.2 (A), R-SW9.2
unnamed: R-D10.2 (A), R-SW10.2
unnamed: R-D11.2 (A), R-SW11.2
unnamed: R-D12.2 (A), R-SW12.2
unnamed: R-D13.2 (A), R-SW13.2
unnamed: R-D14.2 (A), R-SW14.2
unnamed: R-D15.2 (A), R-TS-LED-DOWN1.2
unnamed: R-D16.2 (A), R-SW16.2
unnamed: R-D17.2 (A), R-SW17.2
unnamed: R-D18.2 (A), R-SW18.2
unnamed: R-D19.2 (A), R-SW19.2
unnamed: R-D20.2 (A), R-SW20.2
unnamed: R-D21.2 (A), R-SW21.2
unnamed: R-D22.2 (A), R-SW22.2
unnamed: R-D23.2 (A), R-SW23.2
unnamed: R-D24.2 (A), R-SW24.2
unnamed: R-D25.2 (A), R-SW25.2
unnamed: R-D26.2 (A), R-SW26.2
unnamed: R-D27.2 (A), R-SW27.2
unnamed: R-D28.2 (A), R-SW28.2
unnamed: R-D29.2 (A), R-SW29.2
unnamed: R-D30.2 (A), R-SW30.2
unnamed: R-D31.2 (A), R-SW31.2
unnamed: R-D32.2 (A), R-SW32.2
unnamed: R-D33.2 (A), R-SW33.2
unnamed: R-D34.2 (A), R-SW34.2
unnamed: R-D35.2 (A), R-SW35.2
unnamed: R-D36.2 (A), R-SW36.2
unnamed: R-K-LED1.4 (DIN), R-K-LED2.2 (DOUT)
unnamed: R-K-LED2.4 (DIN), R-K-LED3.2 (DOUT)
unnamed: R-K-LED3.4 (DIN), R-K-LED4.2 (DOUT)
unnamed: R-K-LED4.4 (DIN), R-K-LED5.2 (DOUT)
unnamed: R-K-LED5.4 (DIN), R-K-LED6.2 (DOUT)
unnamed: R-K-LED6.4 (DIN), R-K-LED7.2 (DOUT)
unnamed: R-K-LED10.2 (DOUT), R-K-LED11.4 (DIN)
unnamed: R-K-LED9.2 (DOUT), R-K-LED10.4 (DIN)
unnamed: R-K-LED11.2 (DOUT), R-K-LED12.4 (DIN)
unnamed: R-K-LED12.2 (DOUT), R-K-LED13.4 (DIN)
unnamed: R-K-LED13.2 (DOUT), R-K-LED14.4 (DIN)
unnamed: R-K-LED7.4 (DIN), R-K-LED14.2 (DOUT)
unnamed: R-K-LED9.4 (DIN), R-K-LED16.2 (DOUT)
unnamed: R-K-LED16.4 (DIN), R-K-LED17.2 (DOUT)
unnamed: R-K-LED17.4 (DIN), R-K-LED18.2 (DOUT)
unnamed: R-K-LED18.4 (DIN), R-K-LED19.2 (DOUT)
unnamed: R-K-LED19.4 (DIN), R-K-LED20.2 (DOUT)
unnamed: R-K-LED20.4 (DIN), R-K-LED21.2 (DOUT)
unnamed: R-K-LED21.4 (DIN), R-K-LED29.2 (DOUT)
unnamed: R-K-LED22.2 (DOUT), R-K-LED23.4 (DIN)
unnamed: R-K-LED22.4 (DIN), R-K-LED30.2 (DOUT)
unnamed: R-K-LED23.2 (DOUT), R-K-LED24.4 (DIN)
unnamed: R-K-LED24.2 (DOUT), R-K-LED25.4 (DIN)
unnamed: R-K-LED25.2 (DOUT), R-K-LED26.4 (DIN)
unnamed: R-K-LED26.2 (DOUT), R-K-LED27.4 (DIN)
unnamed: R-K-LED27.2 (DOUT), R-K-LED28.4 (DIN)
unnamed: R-K-LED28.2 (DOUT), R-K-LED29.4 (DIN)
unnamed: R-K-LED30.4 (DIN), R-K-LED31.2 (DOUT)
unnamed: R-K-LED31.4 (DIN), R-K-LED32.2 (DOUT)
unnamed: R-K-LED32.4 (DIN), R-K-LED33.2 (DOUT)
unnamed: R-K-LED33.4 (DIN), R-K-LED34.2 (DOUT)
unnamed: R-K-LED34.4 (DIN), R-K-LED35.2 (DOUT)
unnamed: R-K-LED35.4 (DIN), R-K-LED36.2 (DOUT)
unnamed: R-K-LED36.4 (DIN), R-UG-LED6.2 (DOUT)
unnamed: R-UG-LED0.2 (DOUT), R-UG-LED1.4 (DIN)
unnamed: R-UG-LED1.2 (DOUT), R-UG-LED2.4 (DIN)
unnamed: R-UG-LED2.2 (DOUT), R-UG-LED3.4 (DIN)
unnamed: R-UG-LED3.2 (DOUT), R-UG-LED4.4 (DIN)
unnamed: R-UG-LED4.2 (DOUT), R-UG-LED5.4 (DIN)
unnamed: R-UG-LED5.2 (DOUT), R-UG-LED6.4 (DIN)
unnamed: R-n!n1.1 (TX0/P0.06), R-n!n-L-Adapter1.1
unnamed: R-n!n1.2 (RX1/P0.08), R-n!n-L-Adapter1.2
unnamed: R-n!n1.5 (P0.17), R-n!n-L-Adapter1.5
unnamed: R-n!n1.6 (P0.20), R-n!n-L-Adapter1.6
unnamed: R-n!n1.7 (P0.22), R-n!n-L-Adapter1.7
unnamed: R-n!n1.8 (P0.24), R-n!n-L-Adapter1.8
unnamed: R-n!n1.9 (P1.00), R-n!n-L-Adapter1.9
unnamed: R-n!n1.10 (P0.11), R-n!n-L-Adapter1.10
unnamed: R-n!n1.11 (P1.04), R-n!n-L-Adapter1.11
unnamed: R-n!n1.12 (P1.06), R-n!n-L-Adapter1.12
R-CRQ-VCC-PRESWITCH: R-CRQ-CONN1.12, R-CRQ-JP1.2 (C)
R-LED: R-UG-LED0.4 (DIN), R-n!n-L-Socket1.1
R-LED-VCC: R-K-LED1.1 (VDD), R-K-LED2.1 (VDD), R-K-LED3.1 (VDD), R-K-LED4.1 (VDD), R-K-LED5.1 (VDD), R-K-LED6.1 (VDD), R-K-LED7.1 (VDD), R-K-LED9.1 (VDD), R-K-LED10.1 (VDD), R-K-LED11.1 (VDD), R-K-LED12.1 (VDD), R-K-LED13.1 (VDD), R-K-LED14.1 (VDD), R-K-LED16.1 (VDD), R-K-LED17.1 (VDD), R-K-LED18.1 (VDD), R-K-LED19.1 (VDD), R-K-LED20.1 (VDD), R-K-LED21.1 (VDD), R-K-LED22.1 (VDD), R-K-LED23.1 (VDD), R-K-LED24.1 (VDD), R-K-LED25.1 (VDD), R-K-LED26.1 (VDD), R-K-LED27.1 (VDD), R-K-LED28.1 (VDD), R-K-LED29.1 (VDD), R-K-LED30.1 (VDD), R-K-LED31.1 (VDD), R-K-LED32.1 (VDD), R-K-LED33.1 (VDD), R-K-LED34.1 (VDD), R-K-LED35.1 (VDD), R-K-LED36.1 (VDD), R-SW-LED1.2 (B), R-UG-LED0.1 (VDD), R-UG-LED1.1 (VDD), R-UG-LED2.1 (VDD), R-UG-LED3.1 (VDD), R-UG-LED4.1 (VDD), R-UG-LED5.1 (VDD), R-UG-LED6.1 (VDD)
R-LED-VCC-PRESWITCH: R-LED-JP1.2 (C), R-SW-LED1.3 (C)
R-RAW: J2.12, R-SW-BATT1.2 (B)
R-RE0-A: R-RE0.A, R-n!n-L-Socket1.2
R-RE0-B: R-RE0.B, R-n!n-L-Socket1.7
R-SCL: R-CRQ-CONN1.9, R-n!n-L-Socket1.6
R-SDA: R-CRQ-CONN1.10, R-n!n-L-Socket1.5
R-col0: J2.8, R-RE0.S2, R-SW22.1, R-SW30.1, R-TS-LED-DOWN1.1, R-TS-LED-UP1.1
R-col1: J2.7, R-SW1.1, R-SW23.1, R-SW31.1
R-col2: J2.6, R-SW2.1, R-SW9.1, R-SW16.1, R-SW24.1, R-SW32.1
R-col3: J2.5, R-SW3.1, R-SW10.1, R-SW17.1, R-SW25.1
R-col4: J2.4, R-SW4.1, R-SW11.1, R-SW18.1, R-SW26.1, R-SW33.1
R-col5: J2.3, R-SW5.1, R-SW12.1, R-SW19.1, R-SW27.1, R-SW34.1
R-col6: J2.2, R-SW6.1, R-SW13.1, R-SW20.1, R-SW28.1, R-SW35.1
R-col7: J2.1, R-SW7.1, R-SW14.1, R-SW21.1, R-SW29.1, R-SW36.1
R-reset: J2.10, R-TS-RST1.1
R-row0: R-D0.1 (K), R-D1.1 (K), R-D2.1 (K), R-D3.1 (K), R-D4.1 (K), R-D5.1 (K), R-D6.1 (K), R-D7.1 (K), R-n!n-L-Socket1.8
R-row1: R-D8.1 (K), R-D9.1 (K), R-D10.1 (K), R-D11.1 (K), R-D12.1 (K), R-D13.1 (K), R-D14.1 (K), R-n!n-L-Socket1.9
R-row2: R-D15.1 (K), R-D16.1 (K), R-D17.1 (K), R-D18.1 (K), R-D19.1 (K), R-D20.1 (K), R-D21.1 (K), R-n!n-L-Socket1.10
R-row3: R-D22.1 (K), R-D23.1 (K), R-D24.1 (K), R-D25.1 (K), R-D26.1 (K), R-D27.1 (K), R-D28.1 (K), R-D29.1 (K), R-n!n-L-Socket1.11
R-row4: R-D30.1 (K), R-D31.1 (K), R-D32.1 (K), R-D33.1 (K), R-D34.1 (K), R-D35.1 (K), R-D36.1 (K), R-n!n-L-Socket1.12
VCC: J3.9, L-LED-JP1.1 (A)
VDD: J2.9, R-CRQ-JP1.1 (A), R-LED-JP1.1 (A)

Notes on the sheet:
Column 1
Column 0
Column 3
Column 7
Row 2
Underglow
Row 4
Column 6
Column 5
Row 0
Row 3
Column 4
Column 2
Row 1
